tinkeringjoe/bread-modular/opt/Breakouts/PT8211/PT8211.kicad_pcb

## KiCad design opt/Breakouts/PT8211/PT8211.kicad_pcb (2025-01-01)

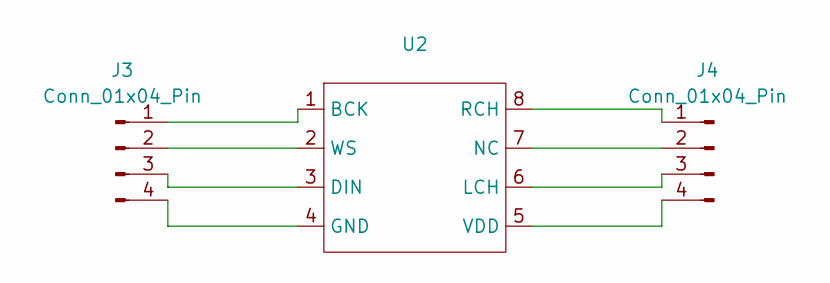
[picture p37: schematic PT8211.kicad_sch]

Parts:
J3, J4: Conn_01x04_Pin; PinSocket_1x04_P2.54mm_Vertical
U2: SOIC-8-1EP_3.9x4.9mm_P1.27mm_EP2.29x3mm

Connections:
unnamed: J3.1, U2.1 (BCK)
unnamed: J3.2, U2.2 (WS)
unnamed: J3.3, U2.3 (DIN)
unnamed: J3.4, U2.4 (GND)
unnamed: J4.1, U2.8 (RCH)
unnamed: J4.2, U2.7 (NC)
unnamed: J4.3, U2.6 (LCH)
unnamed: J4.4, U2.5 (VDD)

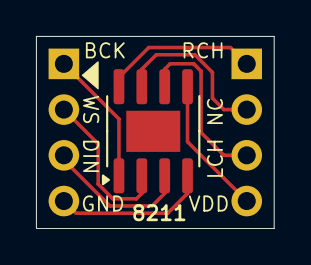
[picture p38: board PT8211.kicad_pcb from above]

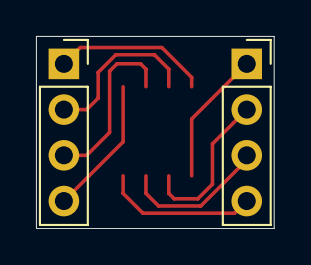
[picture p39: board PT8211.kicad_pcb from below]

Board: 2 copper layers, 13.2 x 10.7 mm, 3 parts (2 on the bottom side), 8 nets.
