tinkeringjoe/bread-modular/opt/Breakouts/Opamps/opamps.kicad_pcb

## KiCad design opt/Breakouts/Opamps/opamps.kicad_pcb (2024-10-20)

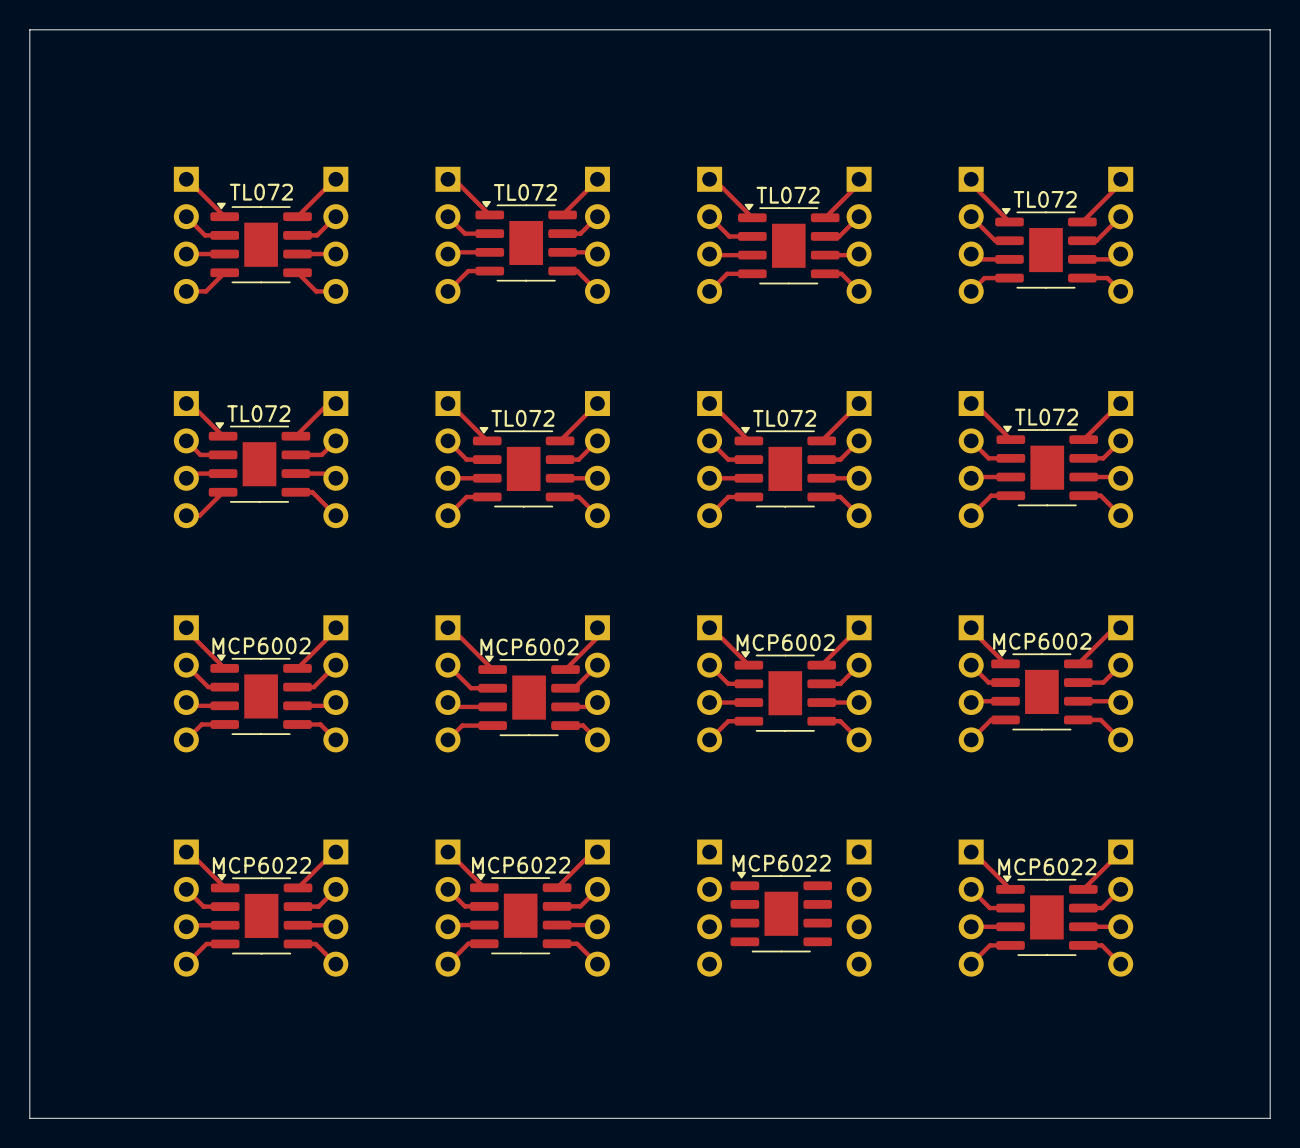
[picture p40: board opamps.kicad_pcb from above]

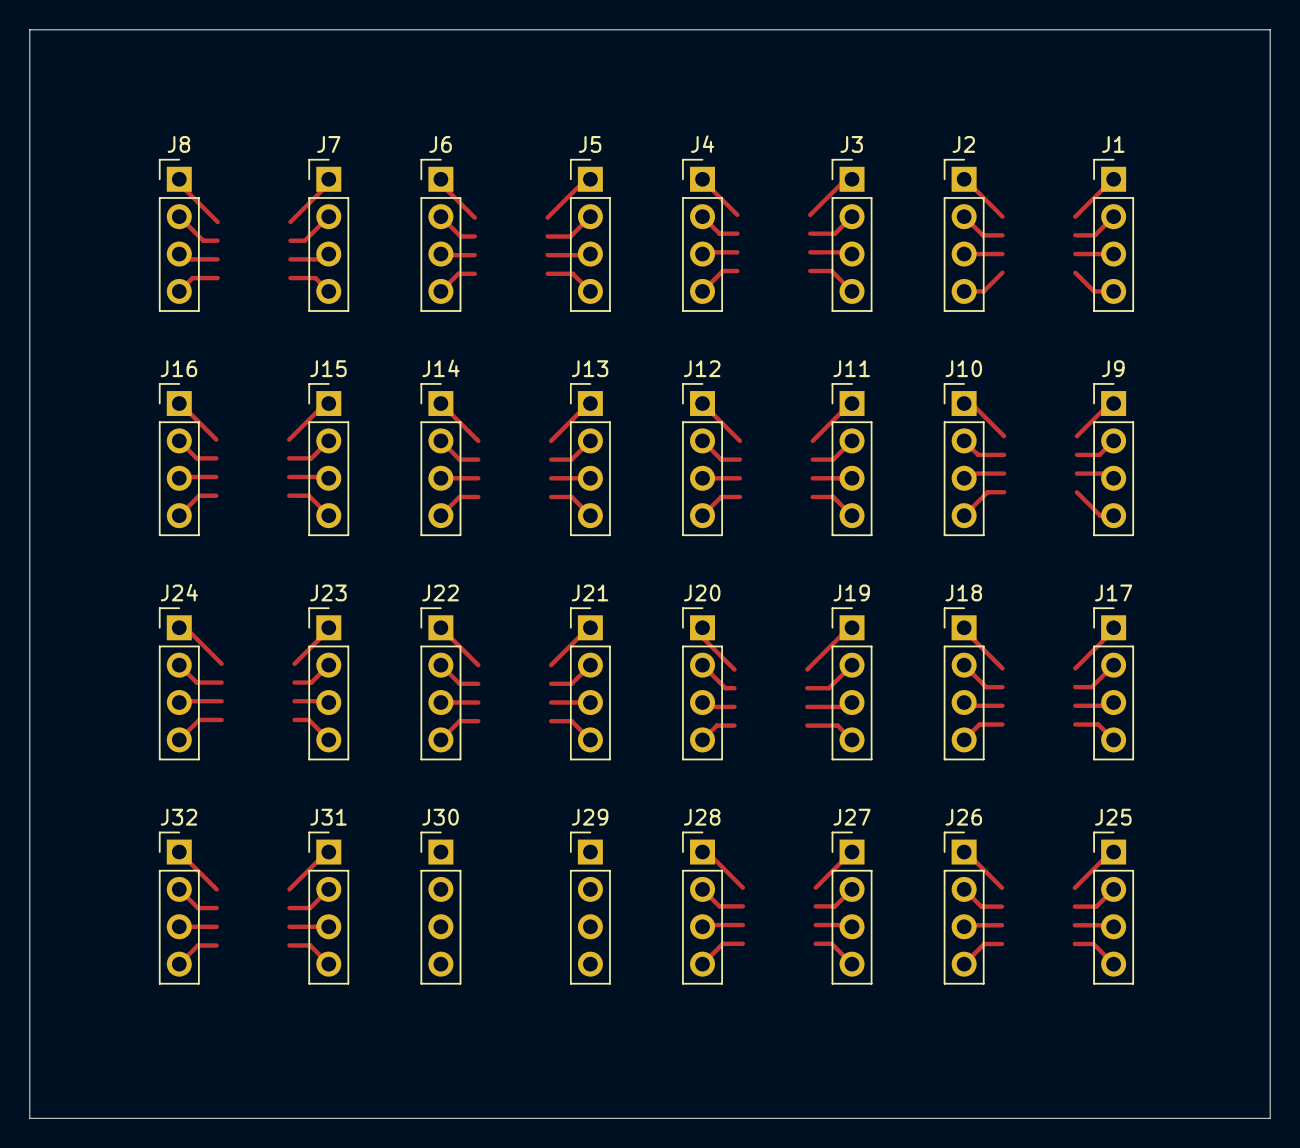
[picture p41: board opamps.kicad_pcb from below]

Board: 2 copper layers, 84.3 x 74.0 mm, 48 parts (32 on the bottom side), 128 nets.

Parts:
J1, J2, J3, J4, J5, J6, J7, J8, J9, J10, J11, J12, J13, J14, J15, J16, J17, J18, J19, J20, J21, J22, J23, J24, J25, J26, J27, J28, J29, J30, J31, J32: Conn_01x04_Pin; PinHeader_1x04_P2.54mm_Vertical
MCP6002, MCP6002#2, MCP6002#3, MCP6002#4: MCP6002-xSN; SOIC-8-1EP_3.9x4.9mm_P1.27mm_EP2.29x3mm
MCP6022, MCP6022#2, MCP6022#3, MCP6022#4: MCP6022; SOIC-8-1EP_3.9x4.9mm_P1.27mm_EP2.29x3mm
TL072, TL072#2, TL072#3, TL072#4, TL072#5, TL072#6, TL072#7, TL072#8: TL072; SOIC-8-1EP_3.9x4.9mm_P1.27mm_EP2.29x3mm

Connections:
unnamed: J1.1, TL072.1
unnamed: J1.2, TL072.2 (-)
unnamed: J1.3, TL072.3 (+)
unnamed: J1.4, TL072.4 (V-)
unnamed: J2.1, TL072.8 (V+)
unnamed: J2.2, TL072.7
unnamed: J2.3, TL072.6 (-)
unnamed: J2.4, TL072.5 (+)
unnamed: J3.1, TL072#2.1
unnamed: J3.2, TL072#2.2 (-)
unnamed: J3.3, TL072#2.3 (+)
unnamed: J3.4, TL072#2.4 (V-)
unnamed: J4.1, TL072#2.8 (V+)
unnamed: J4.2, TL072#2.7
unnamed: J4.3, TL072#2.6 (-)
unnamed: J4.4, TL072#2.5 (+)
unnamed: J5.1, TL072#6.1
unnamed: J5.2, TL072#6.2 (-)
unnamed: J5.3, TL072#6.3 (+)
unnamed: J5.4, TL072#6.4 (V-)
unnamed: J6.1, TL072#6.8 (V+)
unnamed: J6.2, TL072#6.7
unnamed: J6.3, TL072#6.6 (-)
unnamed: J6.4, TL072#6.5 (+)
unnamed: J7.1, TL072#3.1
unnamed: J7.2, TL072#3.2 (-)
unnamed: J7.3, TL072#3.3 (+)
unnamed: J7.4, TL072#3.4 (V-)
unnamed: J8.1, TL072#3.8 (V+)
unnamed: J8.2, TL072#3.7
unnamed: J8.3, TL072#3.6 (-)
unnamed: J8.4, TL072#3.5 (+)
unnamed: J9.1, TL072#8.1
unnamed: J9.2, TL072#8.2 (-)
unnamed: J9.3, TL072#8.3 (+)
unnamed: J9.4, TL072#8.4 (V-)
unnamed: J10.1, TL072#8.8 (V+)
unnamed: J10.2, TL072#8.7
unnamed: J10.3, TL072#8.6 (-)
unnamed: J10.4, TL072#8.5 (+)
unnamed: J11.1, TL072#4.1
unnamed: J11.2, TL072#4.2 (-)
unnamed: J11.3, TL072#4.3 (+)
unnamed: J11.4, TL072#4.4 (V-)
unnamed: J12.1, TL072#4.8 (V+)
unnamed: J12.2, TL072#4.7
unnamed: J12.3, TL072#4.6 (-)
unnamed: J12.4, TL072#4.5 (+)
unnamed: J13.1, TL072#7.1
unnamed: J13.2, TL072#7.2 (-)
unnamed: J13.3, TL072#7.3 (+)
unnamed: J13.4, TL072#7.4 (V-)
unnamed: J14.1, TL072#7.8 (V+)
unnamed: J14.2, TL072#7.7
unnamed: J14.3, TL072#7.6 (-)
unnamed: J14.4, TL072#7.5 (+)
unnamed: J15.1, TL072#5.1
unnamed: J15.2, TL072#5.2 (-)
unnamed: J15.3, TL072#5.3 (+)
unnamed: J15.4, TL072#5.4 (V-)
unnamed: J16.1, TL072#5.8 (V+)
unnamed: J16.2, TL072#5.7
unnamed: J16.3, TL072#5.6 (-)
unnamed: J16.4, TL072#5.5 (+)
unnamed: J17.1, MCP6002#3.1
unnamed: J17.2, MCP6002#3.2 (-)
unnamed: J17.3, MCP6002#3.3 (+)
unnamed: J17.4, MCP6002#3.4 (V-)
unnamed: J18.1, MCP6002#3.8 (V+)
unnamed: J18.2, MCP6002#3.7
unnamed: J18.3, MCP6002#3.6 (-)
unnamed: J18.4, MCP6002#3.5 (+)
unnamed: J19.1, MCP6002#2.1
unnamed: J19.2, MCP6002#2.2 (-)
unnamed: J19.3, MCP6002#2.3 (+)
unnamed: J19.4, MCP6002#2.4 (V-)
unnamed: J20.1, MCP6002#2.8 (V+)
unnamed: J20.2, MCP6002#2.7
unnamed: J20.3, MCP6002#2.6 (-)
unnamed: J20.4, MCP6002#2.5 (+)
unnamed: J21.1, MCP6002.1
unnamed: J21.2, MCP6002.2 (-)
unnamed: J21.3, MCP6002.3 (+)
unnamed: J21.4, MCP6002.4 (V-)
unnamed: J22.1, MCP6002.8 (V+)
unnamed: J22.2, MCP6002.7
unnamed: J22.3, MCP6002.6 (-)
unnamed: J22.4, MCP6002.5 (+)
unnamed: J23.1, MCP6002#4.1
unnamed: J23.2, MCP6002#4.2 (-)
unnamed: J23.3, MCP6002#4.3 (+)
unnamed: J23.4, MCP6002#4.4 (V-)
unnamed: J24.1, MCP6002#4.8 (V+)
unnamed: J24.2, MCP6002#4.7
unnamed: J24.3, MCP6002#4.6 (-)
unnamed: J24.4, MCP6002#4.5 (+)
unnamed: J25.1, MCP6022#3.1
unnamed: J25.2, MCP6022#3.2 (-)
unnamed: J25.3, MCP6022#3.3 (+)
unnamed: J25.4, MCP6022#3.4 (V-)
unnamed: J26.1, MCP6022#3.8 (V+)
unnamed: J26.2, MCP6022#3.7
unnamed: J26.3, MCP6022#3.6 (-)
unnamed: J26.4, MCP6022#3.5 (+)
unnamed: J27.1, MCP6022.1
unnamed: J27.2, MCP6022.2 (-)
unnamed: J27.3, MCP6022.3 (+)
unnamed: J27.4, MCP6022.4 (V-)
unnamed: J28.1, MCP6022.8 (V+)
unnamed: J28.2, MCP6022.7
unnamed: J28.3, MCP6022.6 (-)
unnamed: J28.4, MCP6022.5 (+)
unnamed: J29.1, MCP6022#2.1
unnamed: J29.2, MCP6022#2.2 (-)
unnamed: J29.3, MCP6022#2.3 (+)
unnamed: J29.4, MCP6022#2.4 (V-)
unnamed: J30.1, MCP6022#2.8 (V+)
unnamed: J30.2, MCP6022#2.7
unnamed: J30.3, MCP6022#2.6 (-)
unnamed: J30.4, MCP6022#2.5 (+)
unnamed: J31.1, MCP6022#4.1
unnamed: J31.2, MCP6022#4.2 (-)
unnamed: J31.3, MCP6022#4.3 (+)
unnamed: J31.4, MCP6022#4.4 (V-)
unnamed: J32.1, MCP6022#4.8 (V+)
unnamed: J32.2, MCP6022#4.7
unnamed: J32.3, MCP6022#4.6 (-)
unnamed: J32.4, MCP6022#4.5 (+)
