tinkeringjoe/bread-modular/opt/Breakouts/Attiny1616/MCUs.kicad_pcb

## KiCad design opt/Breakouts/Attiny1616/MCUs.kicad_pcb (2024-11-20)

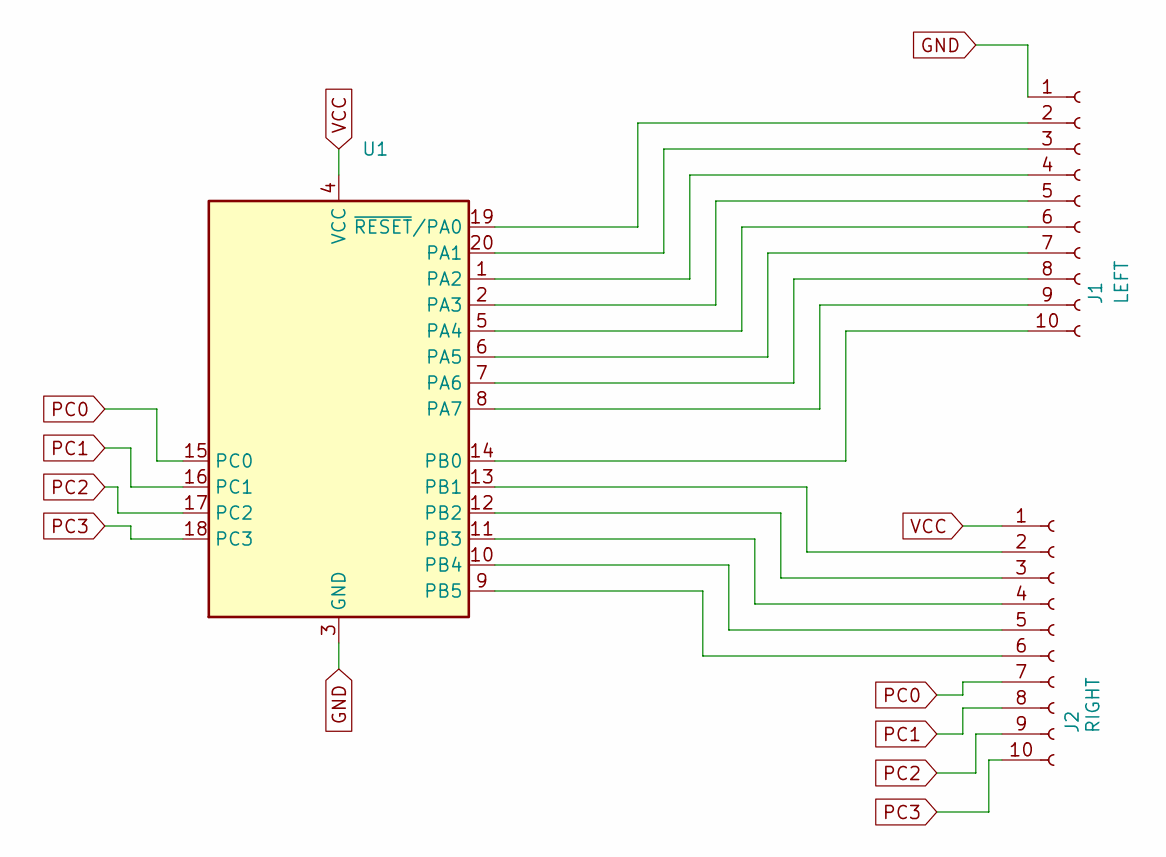
[picture p42: schematic MCUs.kicad_sch]

Parts:
J1: LEFT; PinSocket_1x10_P2.54mm_Vertical
J2: RIGHT; PinSocket_1x10_P2.54mm_Vertical
U1: ATtiny1616-M; VQFN-20-1EP_3x3mm_P0.4mm_EP1.7x1.7mm

Connections:
GND: J1.1, U1.3 (GND), U1.21 (GND)
unnamed: J1.2, U1.19 (~RESET/PA0)
unnamed: J1.3, U1.20 (PA1)
unnamed: J1.4, U1.1 (PA2)
unnamed: J1.5, U1.2 (PA3)
unnamed: J1.6, U1.5 (PA4)
unnamed: J1.7, U1.6 (PA5)
unnamed: J1.8, U1.7 (PA6)
unnamed: J1.9, U1.8 (PA7)
unnamed: J1.10, U1.14 (PB0)
unnamed: J2.2, U1.13 (PB1)
unnamed: J2.3, U1.12 (PB2)
unnamed: J2.4, U1.11 (PB3)
unnamed: J2.5, U1.10 (PB4)
unnamed: J2.6, U1.9 (PB5)
PC0: J2.7, U1.15 (PC0)
PC1: J2.8, U1.16 (PC1)
PC2: J2.9, U1.17 (PC2)
PC3: J2.10, U1.18 (PC3)
VCC: J2.1, U1.4 (VCC)

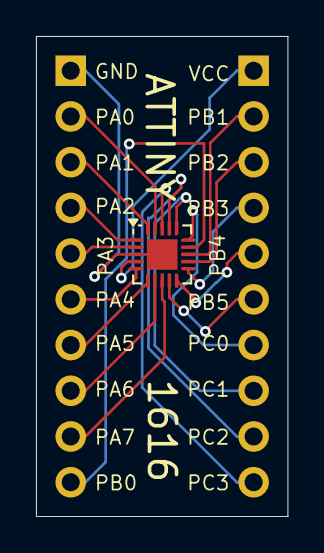
[picture p43: board MCUs.kicad_pcb from above]

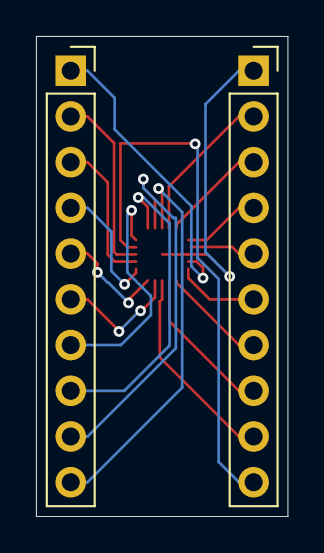
[picture p44: board MCUs.kicad_pcb from below]

Board: 2 copper layers, 14.0 x 26.7 mm, 3 parts (2 on the bottom side), 20 nets.
