tinkeringjoe/bread-modular/modules/drive/drive.kicad_pcb

## KiCad design modules/drive/drive.kicad_pcb (2024-12-27)

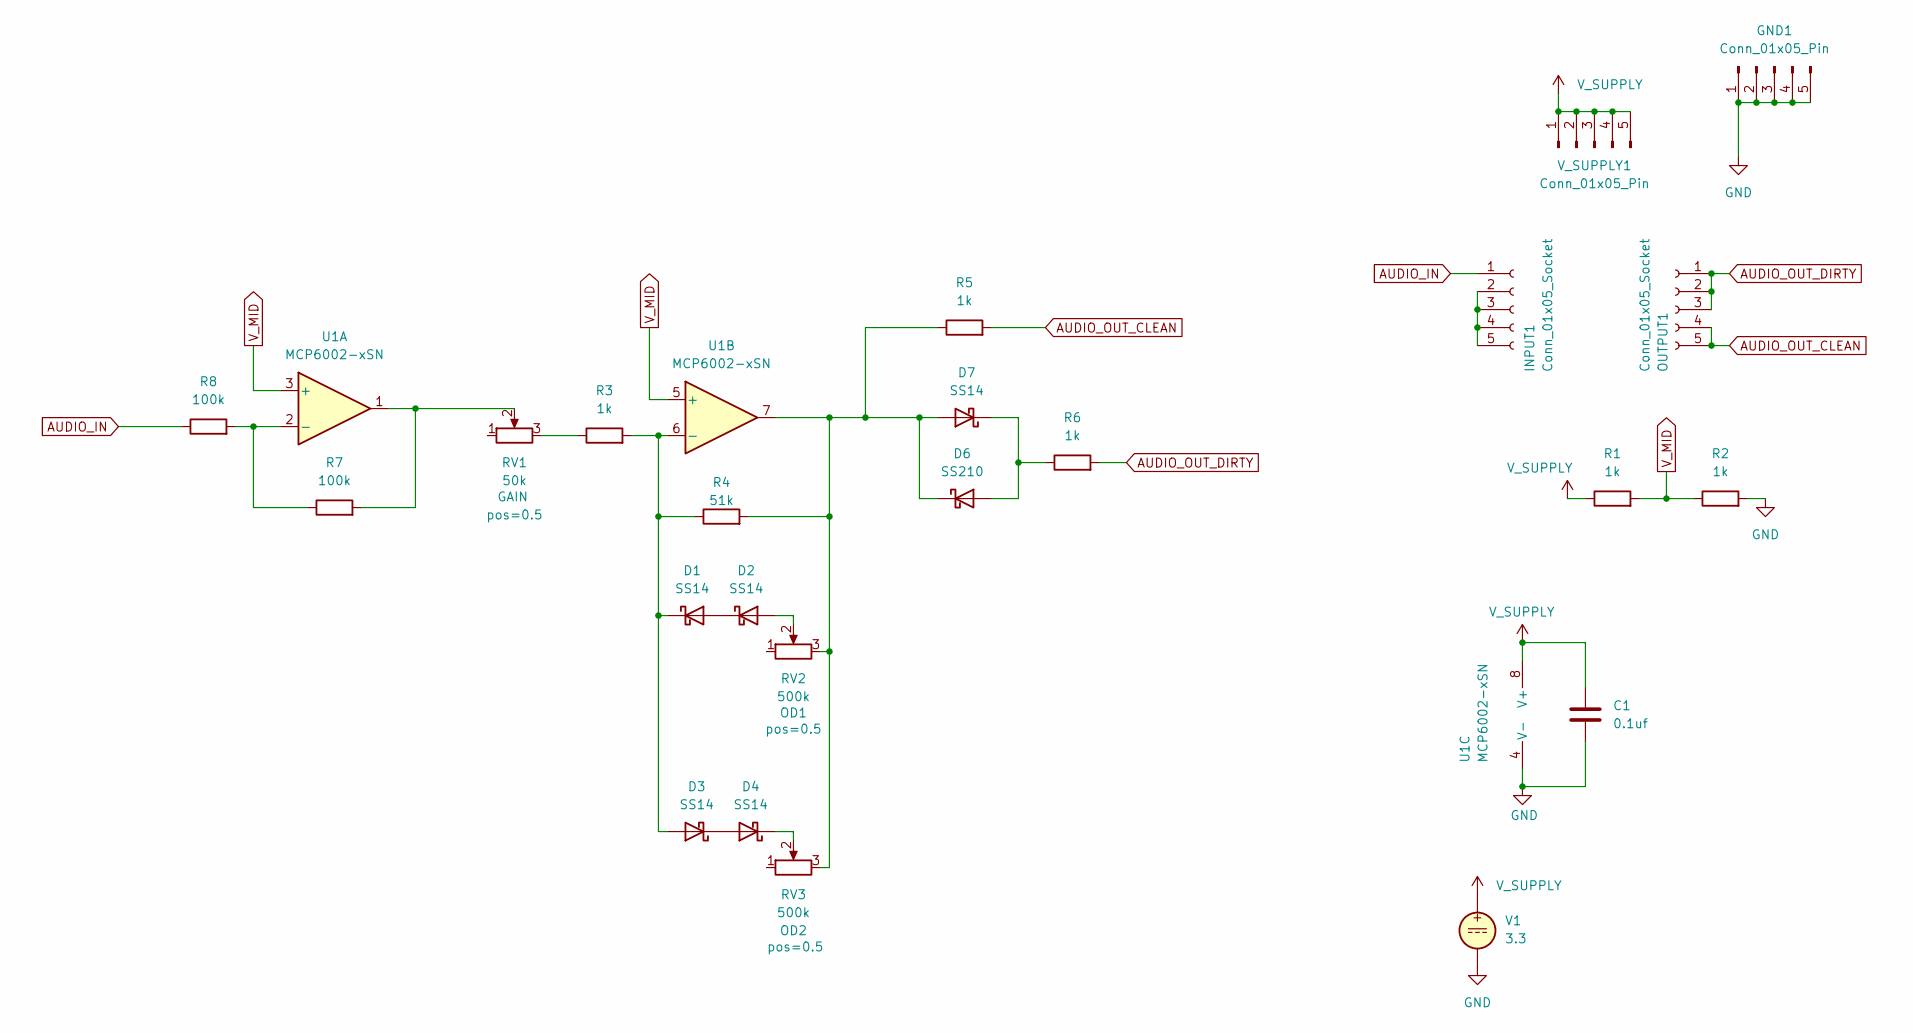
[picture p45: schematic drive.kicad_sch]

Parts:
C1: 0.1uf; C_0402_1005Metric
D1, D2, D3, D4, D7: SS14; D_SMA
D6: SS210; D_SMA
GND1: Conn_01x05_Pin; Power_Connector
INPUT1: Conn_01x05_Socket; PinSocket_1x05_P2.54mm_Vertical
OUTPUT1: Conn_01x05_Socket; PinSocket_1x05_P2.54mm_Vertical
R1, R2, R3, R5, R6: 1k; R_0402_1005Metric
R4: 51k; R_0402_1005Metric
R7, R8: 100k; R_0402_1005Metric
RV1: 50k; Potentiometer_RV09
RV2, RV3: 500k; Potentiometer_RV09
U1: MCP6002-xSN; SOIC-8-1EP_3.9x4.9mm_P1.27mm_EP2.29x3mm
V1: 3.3
V_SUPPLY1: Conn_01x05_Pin; Power_Connector

Connections:
AUDIO_IN: INPUT1.1, R8.1
AUDIO_OUT_CLEAN: OUTPUT1.4, OUTPUT1.5, R5.2
AUDIO_OUT_DIRTY: OUTPUT1.1, OUTPUT1.2, OUTPUT1.3, R6.2
GND: C1.2, GND1.1, GND1.2, GND1.3, GND1.4, GND1.5, R2.2, U1.4 (V-), V1.2
unnamed: D1.2 (A), D2.1 (K)
unnamed: D1.1 (K), D3.2 (A), R3.2, R4.1, U1.6 (-)
unnamed: D2.2 (A), RV2.2
unnamed: D3.1 (K), D4.2 (A)
unnamed: D4.1 (K), RV3.2
unnamed: D6.2 (A), D7.1 (K), R6.1
unnamed: D6.1 (K), D7.2 (A), R4.2, R5.1, RV2.3, RV3.3, U1.7
unnamed: INPUT1.2, INPUT1.3, INPUT1.4, INPUT1.5
unnamed: R3.1, RV1.3
unnamed: R7.2, RV1.2, U1.1
unnamed: R7.1, R8.2, U1.2 (-)
V_MID: R1.2, R2.1, U1.3 (+), U1.5 (+)
V_SUPPLY: C1.1, R1.1, U1.8 (V+), V1.1, V_SUPPLY1.1, V_SUPPLY1.2, V_SUPPLY1.3, V_SUPPLY1.4, V_SUPPLY1.5

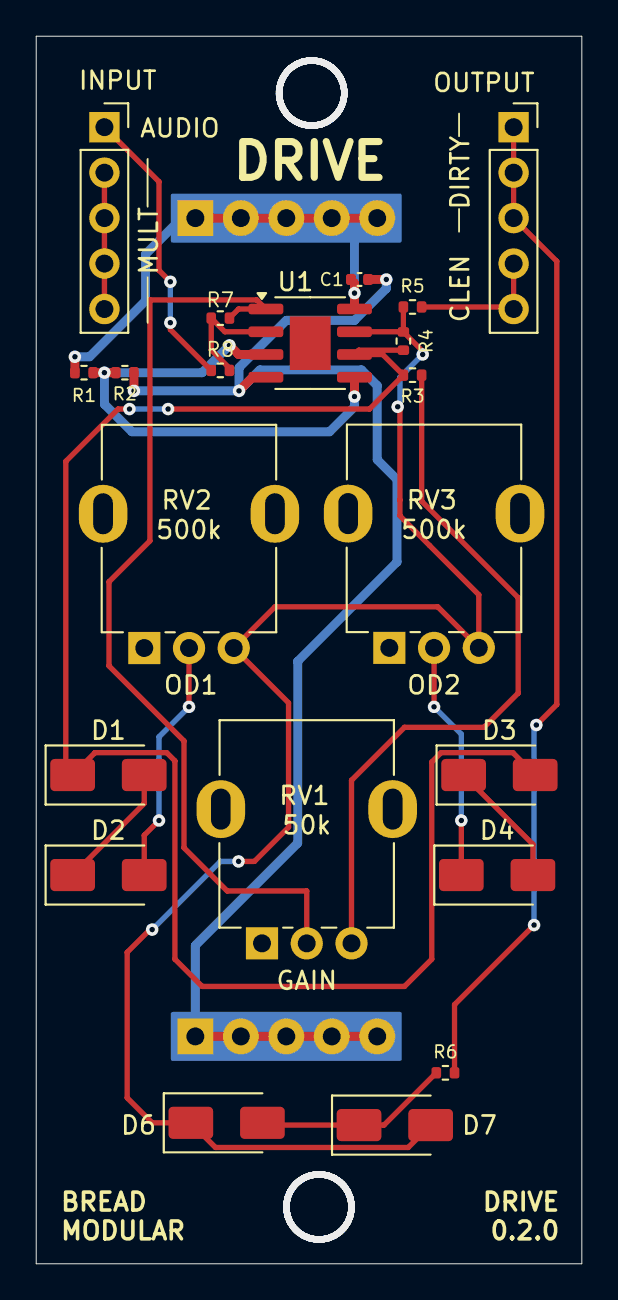
[picture p46: board drive.kicad_pcb from above]

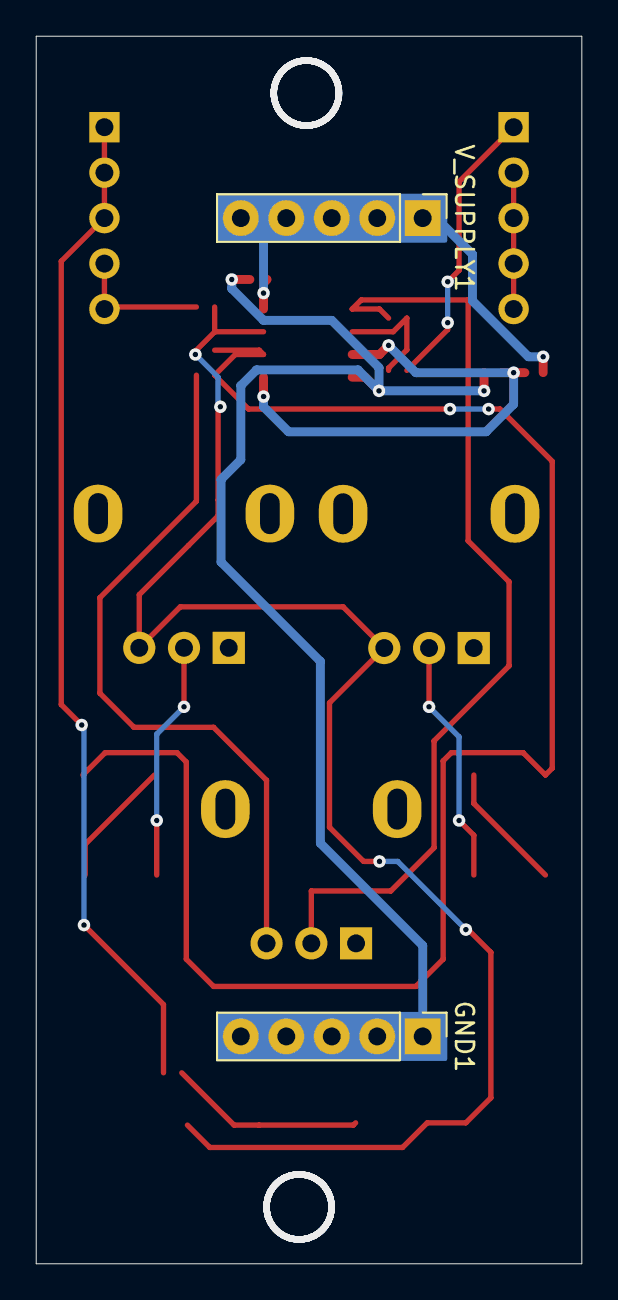
[picture p47: board drive.kicad_pcb from below]

Board: 2 copper layers, 30.5 x 68.6 mm, 23 parts (2 on the bottom side), 17 nets.
