tinkeringjoe/bread-modular/modules/svf/svf.kicad_pcb

## KiCad design modules/svf/svf.kicad_pcb (2024-12-24)

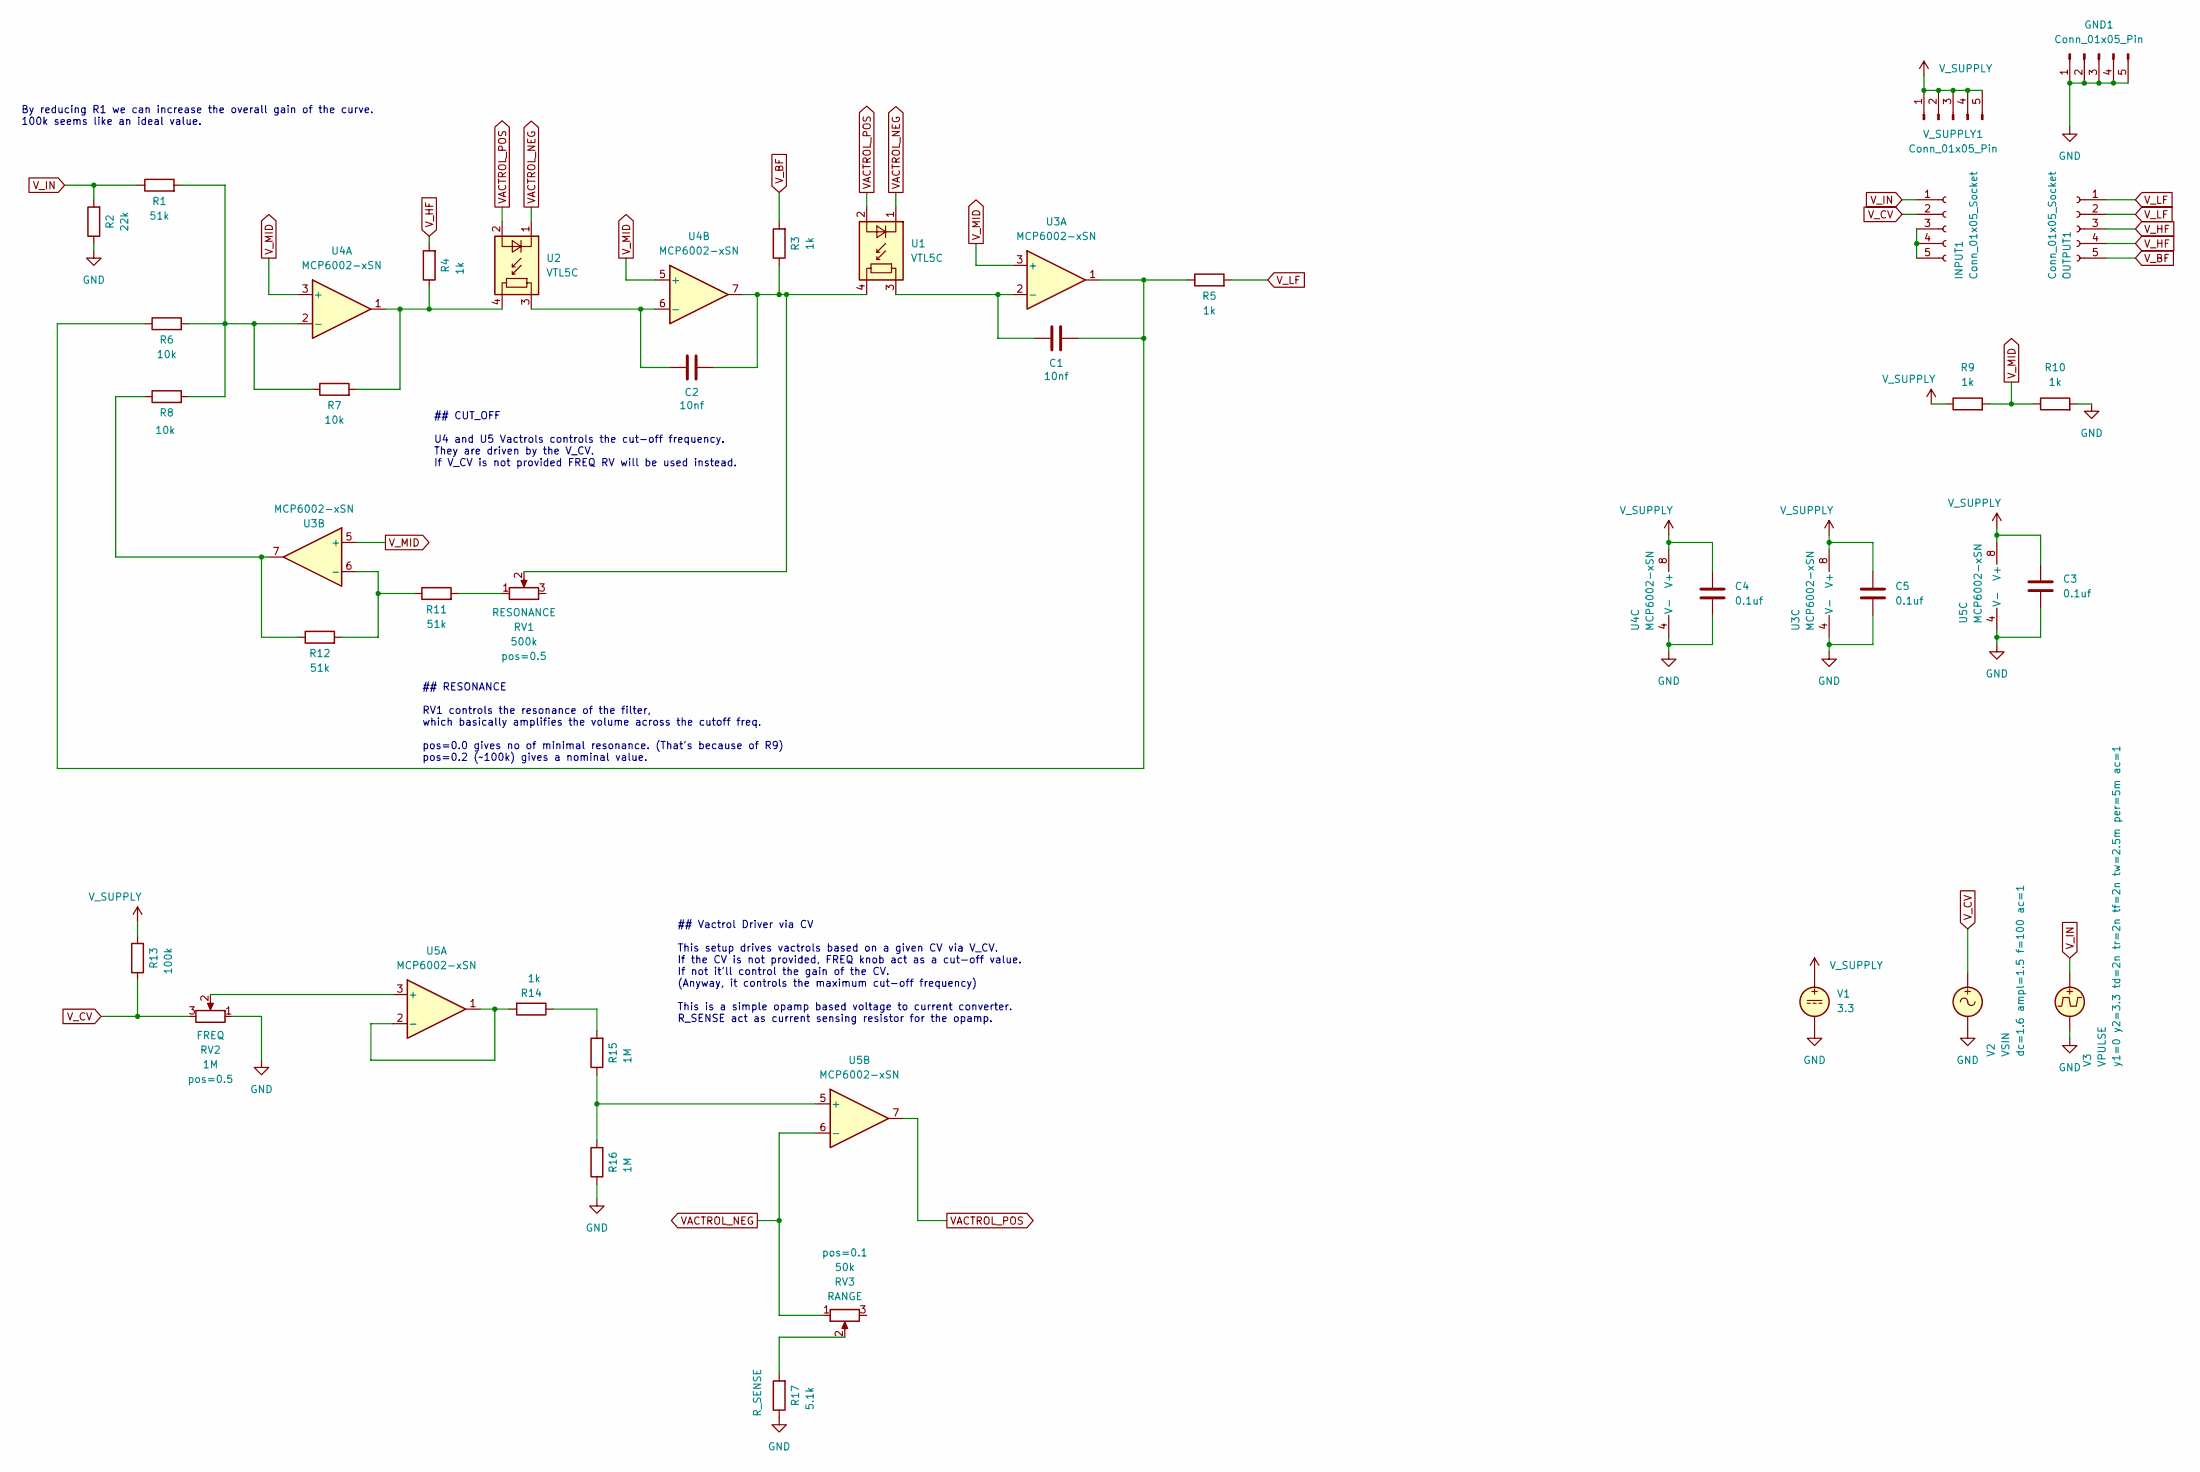
[picture p48: schematic svf.kicad_sch]

Parts:
C1, C2: 10nf; C_0402_1005Metric
C3, C4, C5: 0.1uf; C_0402_1005Metric
GND1: Conn_01x05_Pin; Power_Connector
INPUT1: Conn_01x05_Socket; PinSocket_1x05_P2.54mm_Vertical
OUTPUT1: Conn_01x05_Socket; PinSocket_1x05_P2.54mm_Vertical
R1, R11, R12: 51k; R_0402_1005Metric
R2: 22k; R_0402_1005Metric
R3, R4, R5, R9, R10, R14: 1k; R_0402_1005Metric
R6, R7, R8: 10k; R_0402_1005Metric
R13: 100k; R_0402_1005Metric
R15, R16: 1M; R_0402_1005Metric
R17: 5.1k; R_0402_1005Metric
RV1: 500k; Potentiometer_RV09
RV2: 1M; Potentiometer_RV09
RV3: 50k; Potentiometer_RV09
U1, U2: VTL5C
U3, U4, U5: MCP6002-xSN; SOIC-8-1EP_3.9x4.9mm_P1.27mm_EP2.29x3mm
V1: 3.3
V2: VSIN
V3: VPULSE
V_SUPPLY1: Conn_01x05_Pin; Power_Connector

Connections:
GND: C3.2, C4.2, C5.2, GND1.1, GND1.2, GND1.3, GND1.4, GND1.5, R2.1, R10.2, R16.1, R17.1, RV2.1, U3.4 (V-), U4.4 (V-), U5.4 (V-), V1.2, V2.2, V3.2
unnamed: C1.2, R5.1, R6.1, U3.1
unnamed: C2.2, R3.1, RV1.2, U1.4, U4.7
unnamed: INPUT1.3, INPUT1.4, INPUT1.5
unnamed: R4.1, R7.2, U2.4, U4.1
unnamed: R11.2, RV1.1
unnamed: R8.1, R12.1, U3.7
unnamed: R14.1, R15.2
unnamed: R17.2, RV3.2
unnamed: C1.1, U1.3, U3.2 (-)
unnamed: R11.1, R12.2, U3.6 (-)
unnamed: R1.2, R6.2, R7.1, R8.2, U4.2 (-)
unnamed: C2.1, U2.3, U4.6 (-)
unnamed: RV2.2, U5.3 (+)
unnamed: R14.2, U5.1, U5.2 (-)
unnamed: R15.1, R16.2, U5.5 (+)
VACTROL_NEG: RV3.1, U1.1 (-), U2.1 (-), U5.6 (-)
VACTROL_POS: U1.2 (+), U2.2 (+), U5.7
V_BF: OUTPUT1.5, R3.2
V_CV: INPUT1.2, R13.1, RV2.3, V2.1
V_HF: OUTPUT1.3, OUTPUT1.4, R4.2
V_IN: INPUT1.1, R1.1, R2.2, V3.1
V_LF: OUTPUT1.1, OUTPUT1.2, R5.2
V_MID: R9.2, R10.1, U3.3 (+), U3.5 (+), U4.3 (+), U4.5 (+)
V_SUPPLY: C3.1, C4.1, C5.1, R9.1, R13.2, U3.8 (V+), U4.8 (V+), U5.8 (V+), V1.1, V_SUPPLY1.1, V_SUPPLY1.2, V_SUPPLY1.3, V_SUPPLY1.4, V_SUPPLY1.5

Notes on the sheet:
## Vactrol Driver via CV This setup drives vactrols based on a given CV via V_CV. If the CV is not provided, FREQ knob act as a cut-off value. If not it'll control the gain of the CV. (Anyway, it controls the maximum cut-off frequency) This is a simple opamp based voltage to current converter. R_SE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
## CUT_OFF U4 and U5 Vactrols controls the cut-off frequency. They are driven by the V_CV. If V_CV is not provided FREQ RV will be used instead.
## RESONANCE RV1 controls the resonance of the filter, which basically amplifies the volume across the cutoff freq. pos=0.0 gives no of minimal resonance. (That's because of R9) pos=0.2 (~100k) gives a nominal value.
By reducing R1 we can increase the overall gain of the curve. 100k seems like an ideal value.

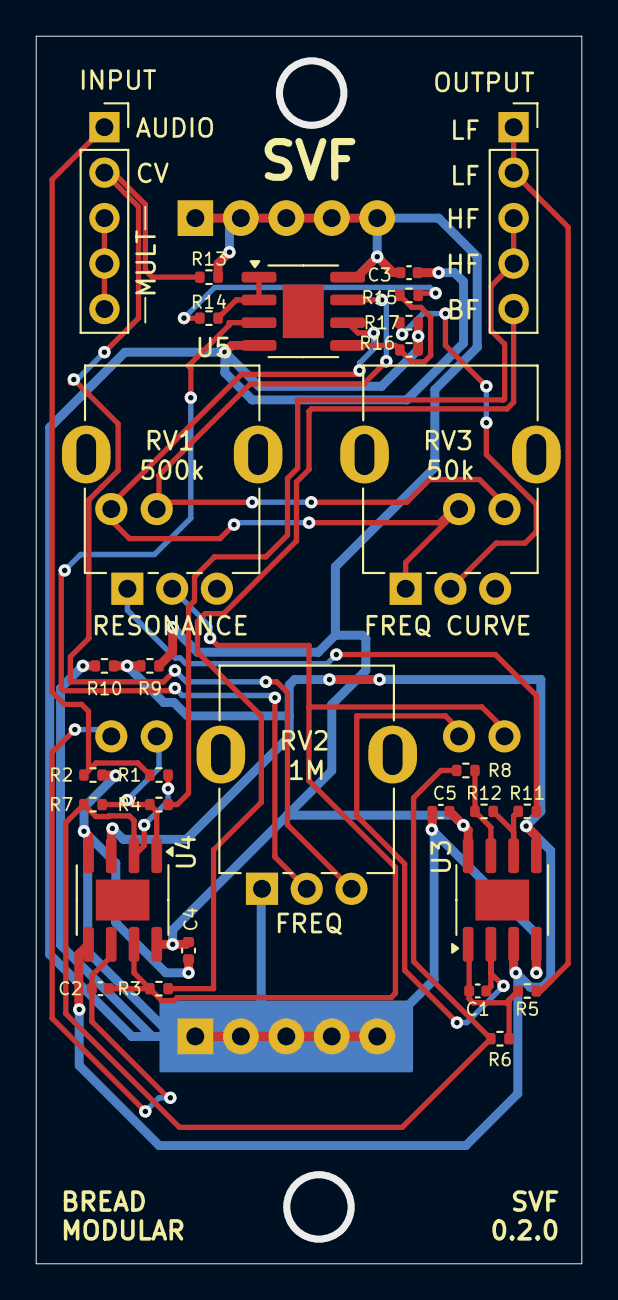
[picture p49: board svf.kicad_pcb from above]

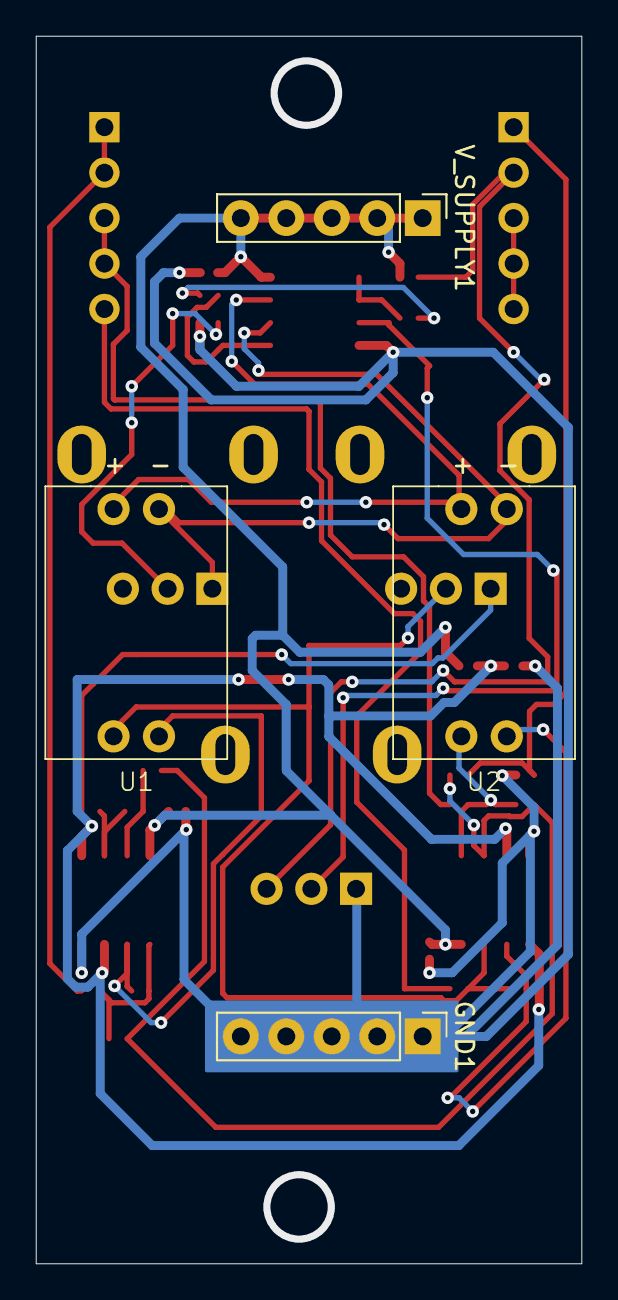
[picture p50: board svf.kicad_pcb from below]

Board: 2 copper layers, 30.5 x 68.6 mm, 34 parts (4 on the bottom side), 25 nets.
