tinkeringjoe/bread-modular/modules/blank/blank.kicad_pcb

## KiCad design modules/blank/blank.kicad_pcb (2024-12-21)

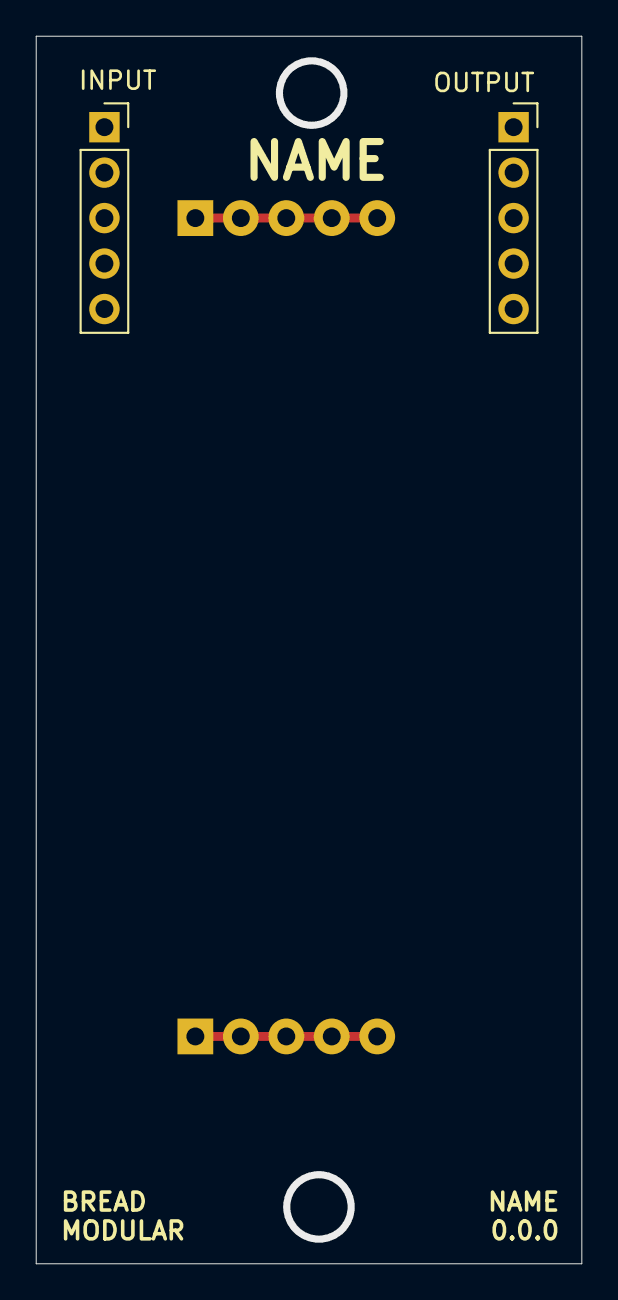
[picture p51: board blank.kicad_pcb from above]

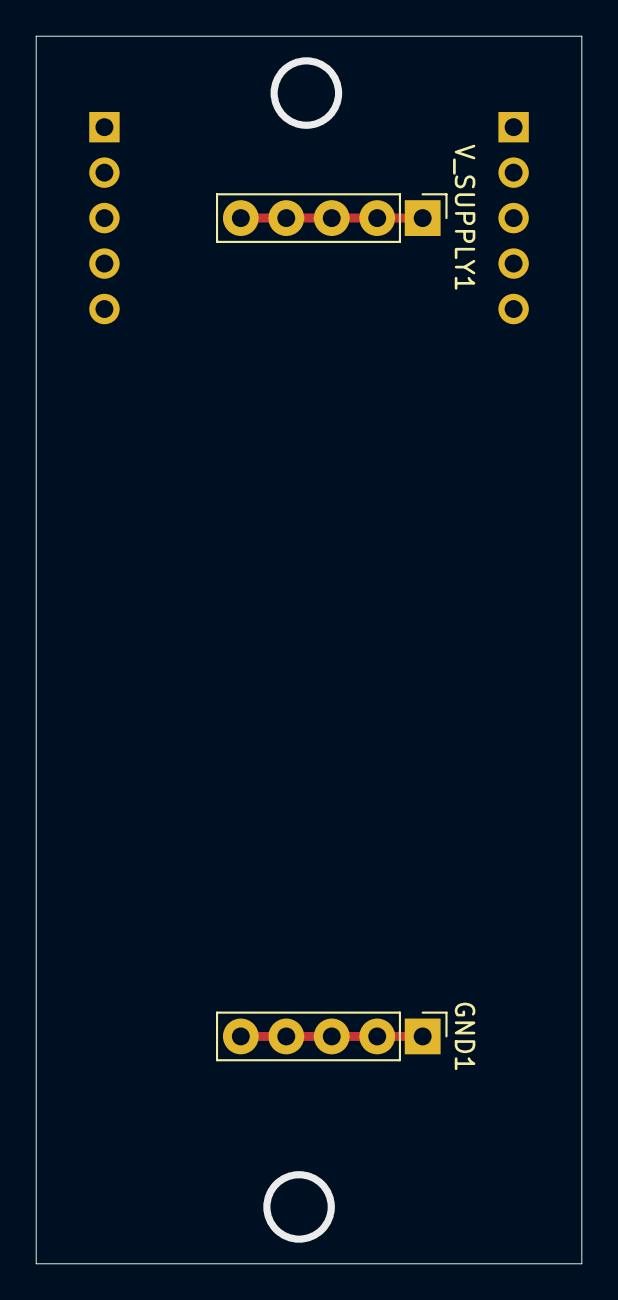
[picture p52: board blank.kicad_pcb from below]

Board: 2 copper layers, 30.5 x 68.6 mm, 4 parts (2 on the bottom side), 2 nets.

Parts:
GND1: Conn_01x05_Pin; Power_Connector
INPUT1: Conn_01x05_Socket; PinSocket_1x05_P2.54mm_Vertical
OUTPUT1: Conn_01x05_Socket; PinSocket_1x05_P2.54mm_Vertical
V_SUPPLY1: Conn_01x05_Pin; Power_Connector

Connections:
GND: GND1.1, GND1.2, GND1.3, GND1.4, GND1.5
V_SUPPLY: V_SUPPLY1.1, V_SUPPLY1.2, V_SUPPLY1.3, V_SUPPLY1.4, V_SUPPLY1.5
