tinkeringjoe/bread-modular/modules/cv_math/cv_math.kicad_pcb

## KiCad design modules/cv_math/cv_math.kicad_pcb (2024-12-15)

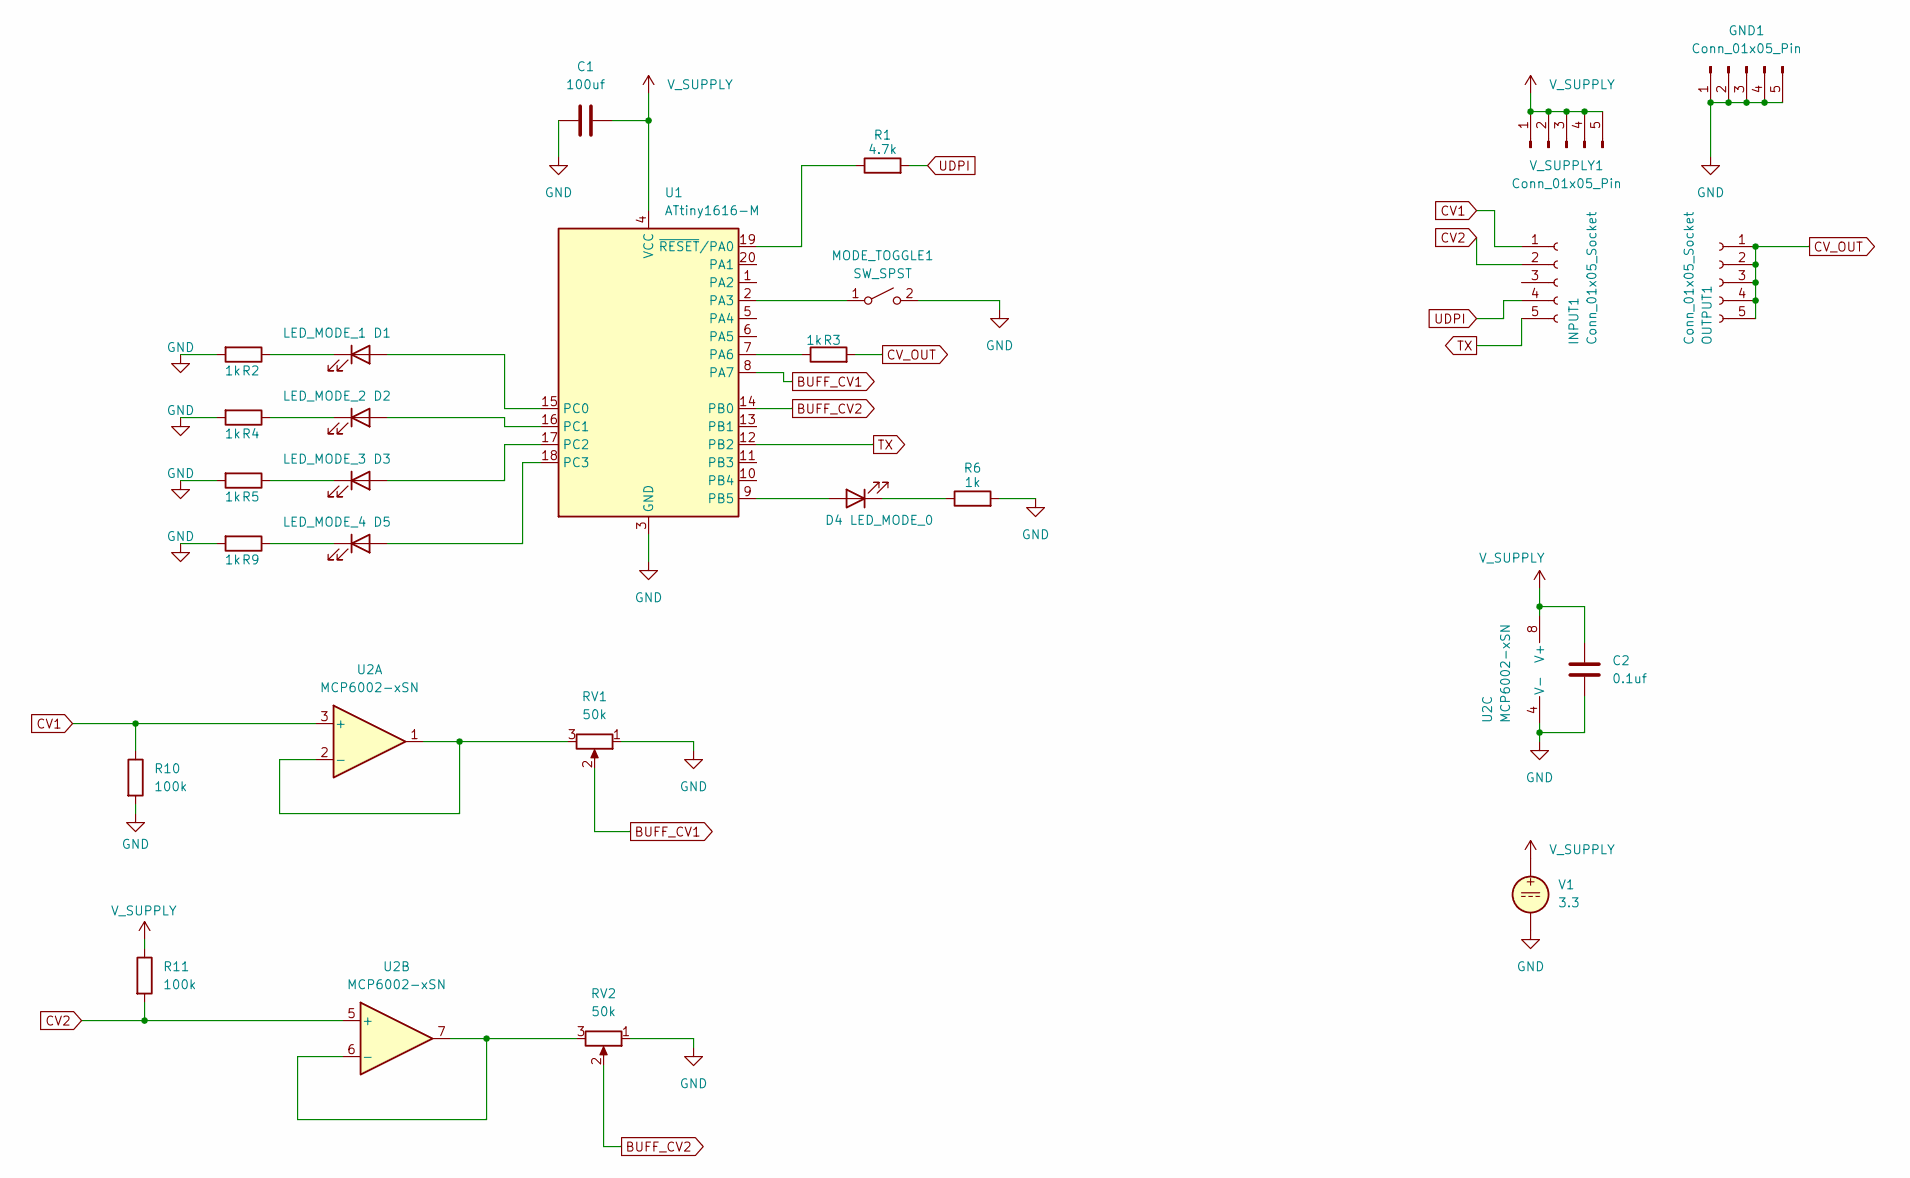
[picture p53: schematic cv_math.kicad_sch]

Parts:
C1: 100uf; C_1206_3216Metric
C2: 0.1uf; C_0402_1005Metric
D1: LED_MODE_1; LED_0603_1608Metric
D2: LED_MODE_2; LED_0603_1608Metric
D3: LED_MODE_3; LED_0603_1608Metric
D4: LED_MODE_0; LED_0603_1608Metric
D5: LED_MODE_4; LED_0603_1608Metric
GND1: Conn_01x05_Pin; Power_Connector
INPUT1: Conn_01x05_Socket; PinSocket_1x05_P2.54mm_Vertical
MODE_TOGGLE1: SW_SPST; SPST_TS-1187A-B-A-B
OUTPUT1: Conn_01x05_Socket; PinSocket_1x05_P2.54mm_Vertical
R1: 4.7k; R_0402_1005Metric
R2, R3, R4, R5, R6, R9: 1k; R_0402_1005Metric
R10, R11: 100k; R_0402_1005Metric
RV1, RV2: 50k; Potentiometer_RV09
U1: ATtiny1616-M; VQFN-20-1EP_3x3mm_P0.4mm_EP1.7x1.7mm
U2: MCP6002-xSN; SOIC-8-1EP_3.9x4.9mm_P1.27mm_EP2.29x3mm
V1: 3.3
V_SUPPLY1: Conn_01x05_Pin; Power_Connector

Connections:
BUFF_CV1: RV1.2, U1.8 (PA7)
BUFF_CV2: RV2.2, U1.14 (PB0)
CV1: INPUT1.1, R10.1, U2.3 (+)
CV2: INPUT1.2, R11.2, U2.5 (+)
CV_OUT: OUTPUT1.1, OUTPUT1.2, OUTPUT1.3, OUTPUT1.4, OUTPUT1.5, R3.2
GND: C1.1, C2.2, GND1.1, GND1.2, GND1.3, GND1.4, GND1.5, MODE_TOGGLE1.2 (B), R2.2, R4.2, R5.2, R6.2, R9.2, R10.2, RV1.1, RV2.1, U1.3 (GND), U1.21 (GND), U2.4 (V-), V1.2
unnamed: D1.2 (A), U1.15 (PC0)
unnamed: D1.1 (K), R2.1
unnamed: D2.2 (A), U1.16 (PC1)
unnamed: D2.1 (K), R4.1
unnamed: D3.2 (A), U1.17 (PC2)
unnamed: D3.1 (K), R5.1
unnamed: D4.2 (A), U1.9 (PB5)
unnamed: D4.1 (K), R6.1
unnamed: D5.2 (A), U1.18 (PC3)
unnamed: D5.1 (K), R9.1
unnamed: MODE_TOGGLE1.1 (A), U1.2 (PA3)
unnamed: R3.1, U1.7 (PA6)
unnamed: R1.1, U1.19 (~RESET/PA0)
unnamed: RV1.3, U2.1, U2.2 (-)
unnamed: RV2.3, U2.6 (-), U2.7
TX: INPUT1.5, U1.12 (PB2)
UDPI: INPUT1.4, R1.2
V_SUPPLY: C1.2, C2.1, R11.1, U1.4 (VCC), U2.8 (V+), V1.1, V_SUPPLY1.1, V_SUPPLY1.2, V_SUPPLY1.3, V_SUPPLY1.4, V_SUPPLY1.5

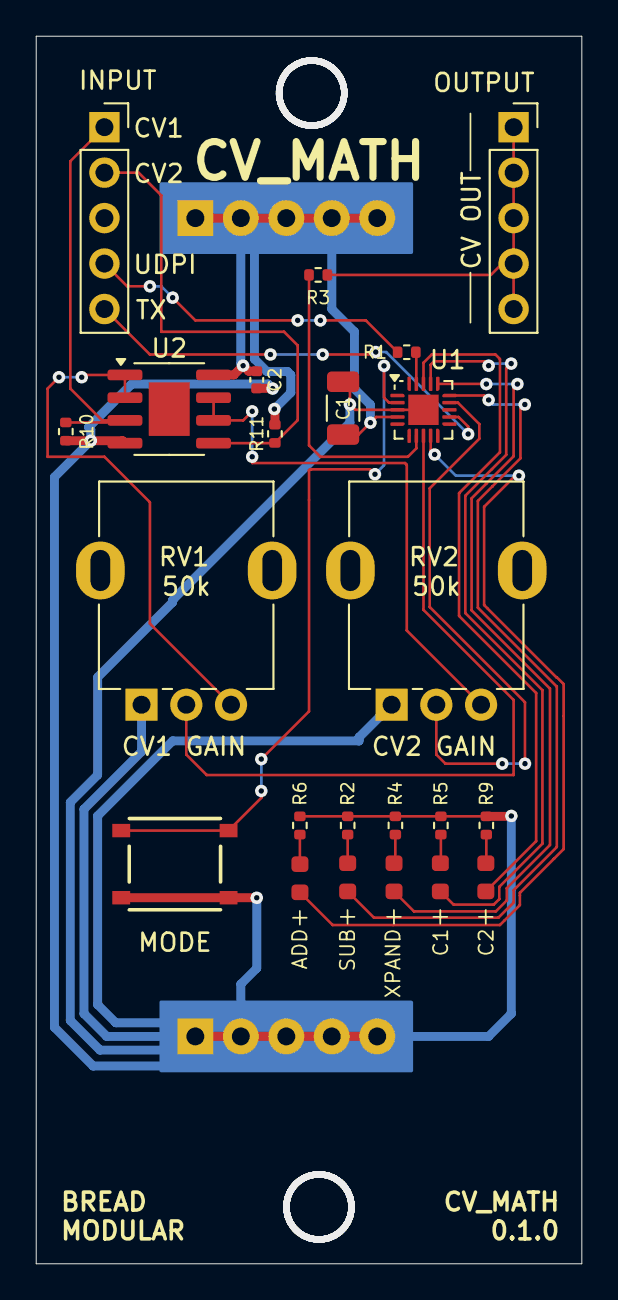
[picture p54: board cv_math.kicad_pcb from above]

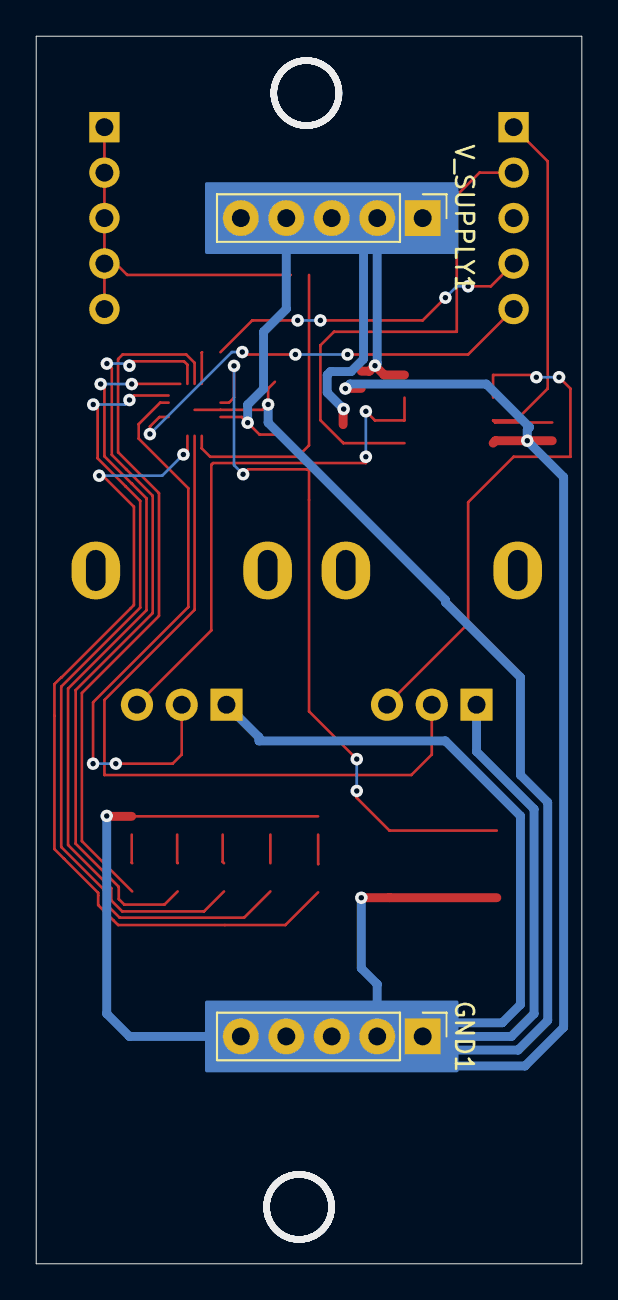
[picture p55: board cv_math.kicad_pcb from below]

Board: 2 copper layers, 30.5 x 68.6 mm, 25 parts (2 on the bottom side), 24 nets.
