tinkeringjoe/bread-modular/modules/noise/noise.kicad_pcb

## KiCad design modules/noise/noise.kicad_pcb (2024-12-09)

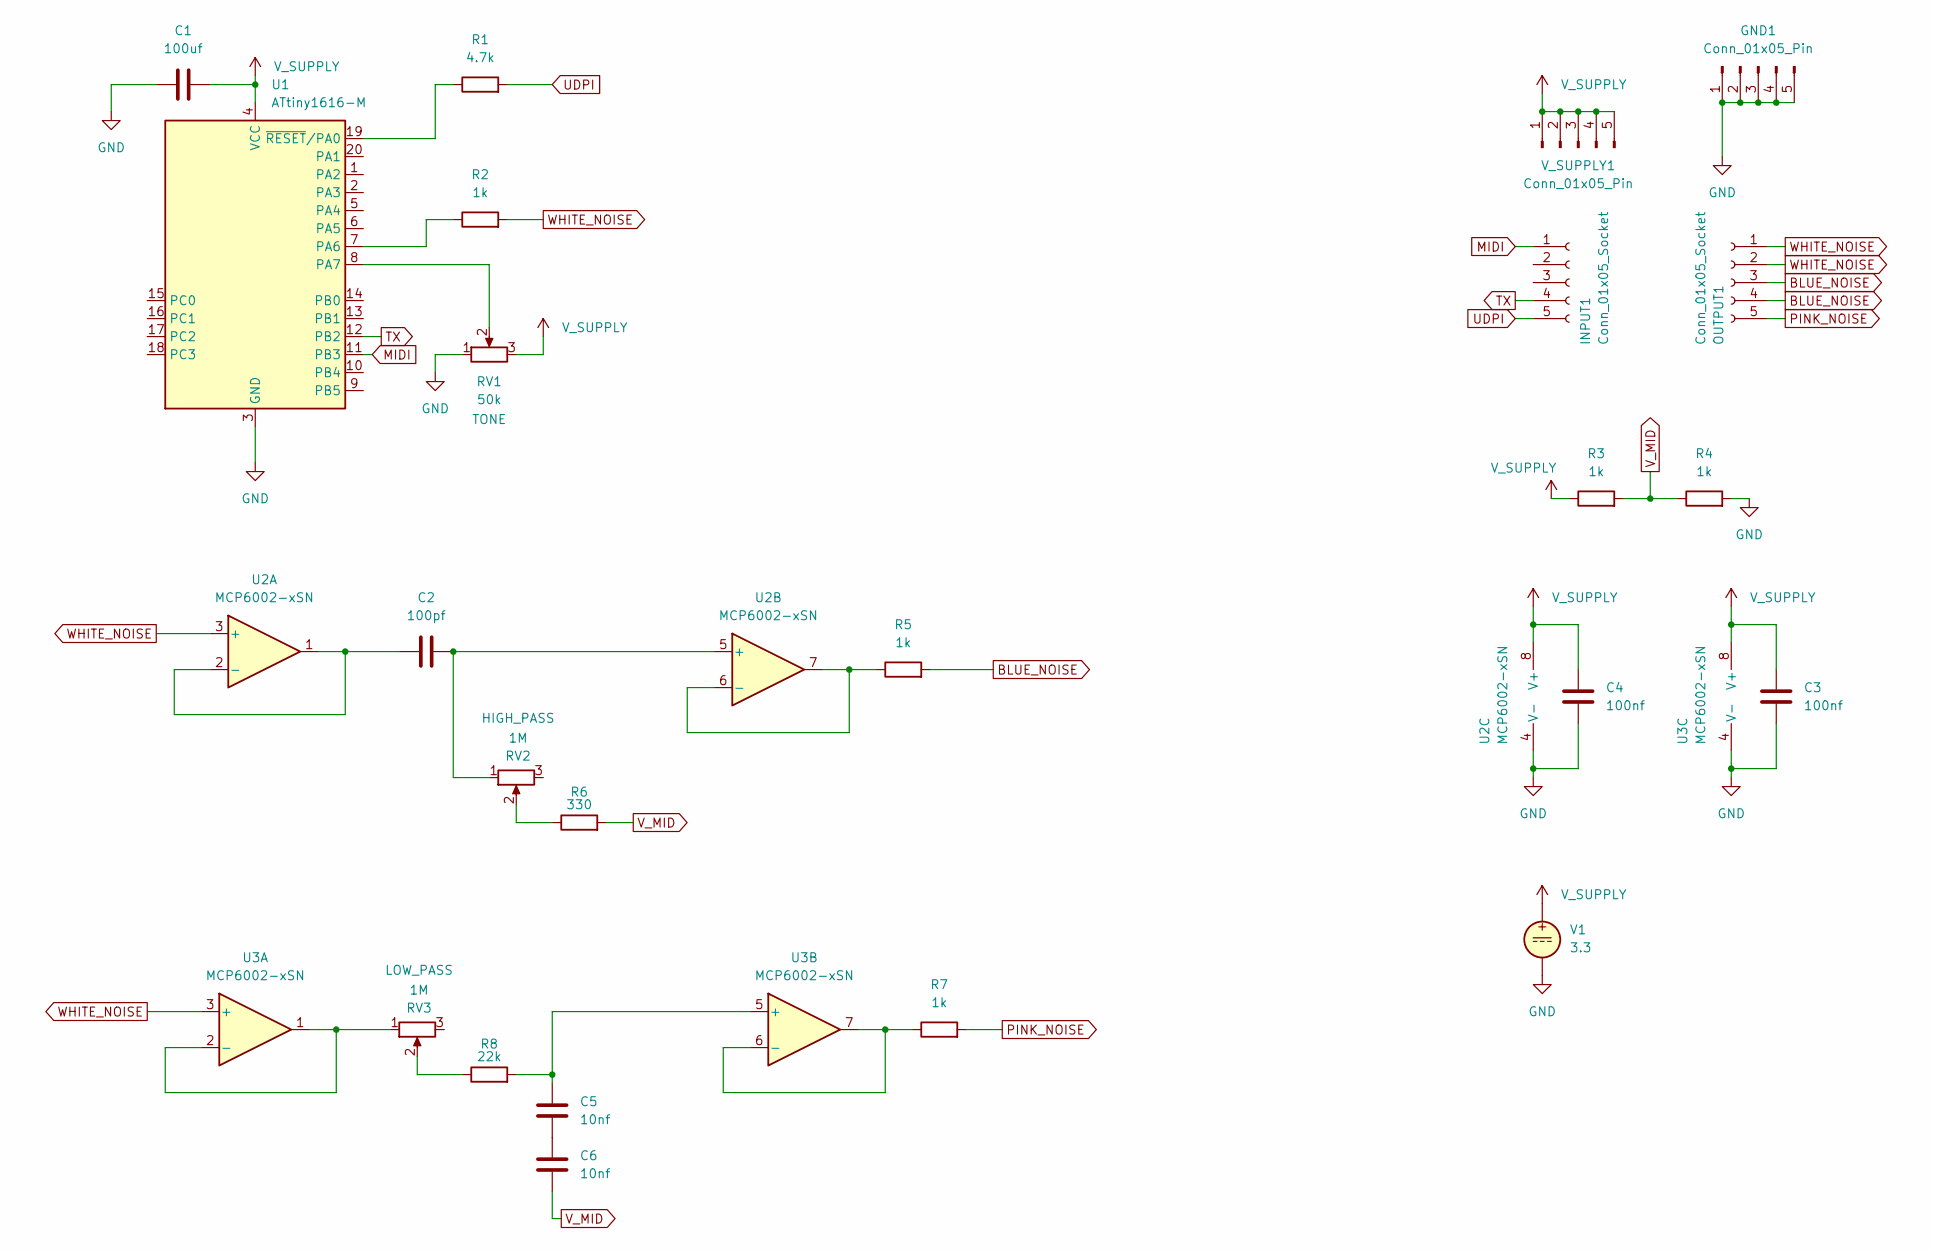
[picture p56: schematic noise.kicad_sch]

Parts:
C1: 100uf; C_1206_3216Metric
C2: 100pf; C_0402_1005Metric
C3, C4: 100nf; C_0402_1005Metric
C5, C6: 10nf; C_0402_1005Metric
GND1: Conn_01x05_Pin; Power_Connector
INPUT1: Conn_01x05_Socket; PinSocket_1x05_P2.54mm_Vertical
OUTPUT1: Conn_01x05_Socket; PinSocket_1x05_P2.54mm_Vertical
R1: 4.7k; R_0402_1005Metric
R2, R3, R4, R5, R7: 1k; R_0402_1005Metric
R6: 330; R_0402_1005Metric
R8: 22k; R_0402_1005Metric
RV1: 50k; Potentiometer_RV09
RV2, RV3: 1M; Potentiometer_RV09
U1: ATtiny1616-M; VQFN-20-1EP_3x3mm_P0.4mm_EP1.7x1.7mm
U2, U3: MCP6002-xSN; SOIC-8-1EP_3.9x4.9mm_P1.27mm_EP2.29x3mm
V1: 3.3
V_SUPPLY1: Conn_01x05_Pin; Power_Connector

Connections:
BLUE_NOISE: OUTPUT1.3, OUTPUT1.4, R5.2
GND: C1.1, C3.1, C4.1, GND1.1, GND1.2, GND1.3, GND1.4, GND1.5, R4.2, RV1.1, U1.3 (GND), U1.21 (GND), U2.4 (V-), U3.4 (V-), V1.2
MIDI: INPUT1.1, U1.11 (PB3)
unnamed: C5.1, C6.2
unnamed: R6.1, RV2.2
unnamed: R8.1, RV3.2
unnamed: R2.1, U1.7 (PA6)
unnamed: RV1.2, U1.8 (PA7)
unnamed: R1.1, U1.19 (~RESET/PA0)
unnamed: C2.1, U2.1, U2.2 (-)
unnamed: C2.2, RV2.1, U2.5 (+)
unnamed: R5.1, U2.6 (-), U2.7
unnamed: RV3.1, U3.1, U3.2 (-)
unnamed: C5.2, R8.2, U3.5 (+)
unnamed: R7.1, U3.6 (-), U3.7
PINK_NOISE: OUTPUT1.5, R7.2
TX: INPUT1.4, U1.12 (PB2)
UDPI: INPUT1.5, R1.2
V_MID: C6.1, R3.2, R4.1, R6.2
V_SUPPLY: C1.2, C3.2, C4.2, R3.1, RV1.3, U1.4 (VCC), U2.8 (V+), U3.8 (V+), V1.1, V_SUPPLY1.1, V_SUPPLY1.2, V_SUPPLY1.3, V_SUPPLY1.4, V_SUPPLY1.5
WHITE_NOISE: OUTPUT1.1, OUTPUT1.2, R2.2, U2.3 (+), U3.3 (+)

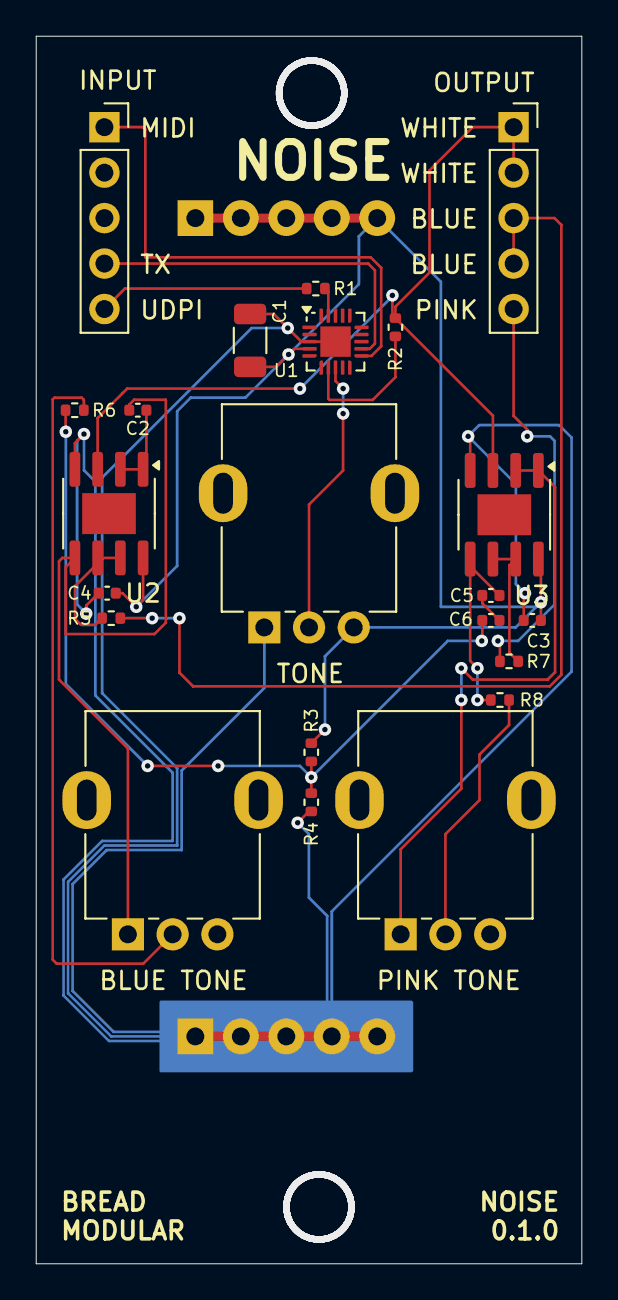
[picture p57: board noise.kicad_pcb from above]

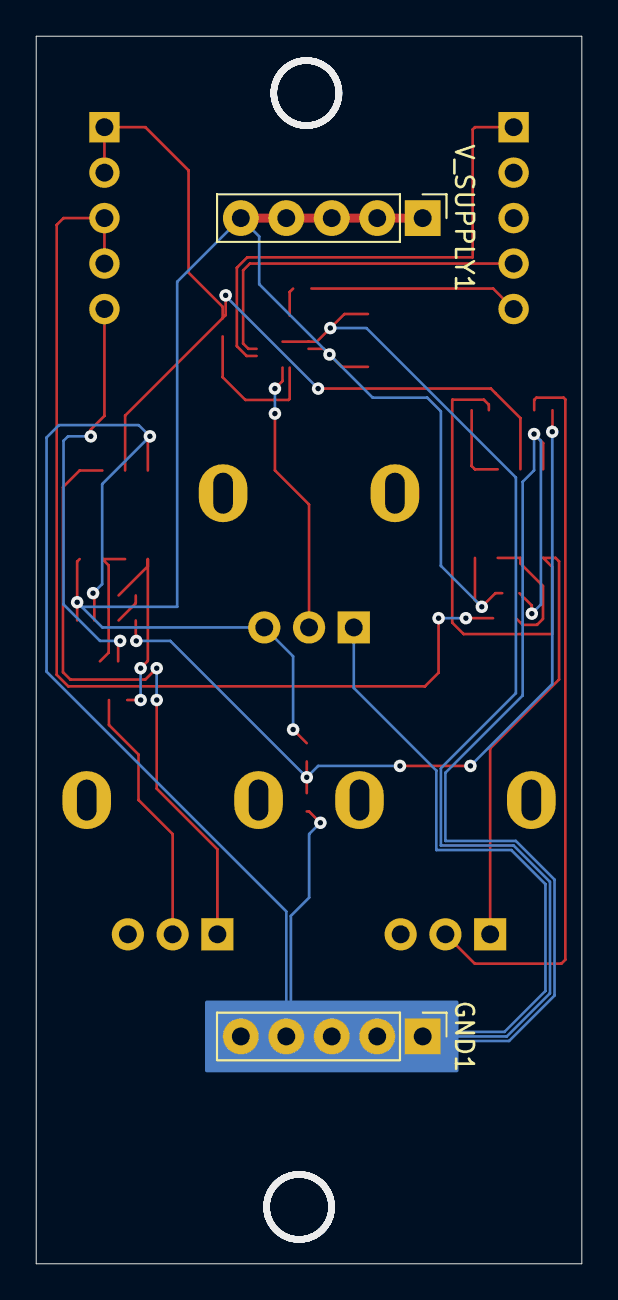
[picture p58: board noise.kicad_pcb from below]

Board: 2 copper layers, 30.5 x 68.6 mm, 24 parts (2 on the bottom side), 21 nets.
