tinkeringjoe/bread-modular/modules/usb_power/usb_power.kicad_pcb

## KiCad design modules/usb_power/usb_power.kicad_pcb (2024-11-24)

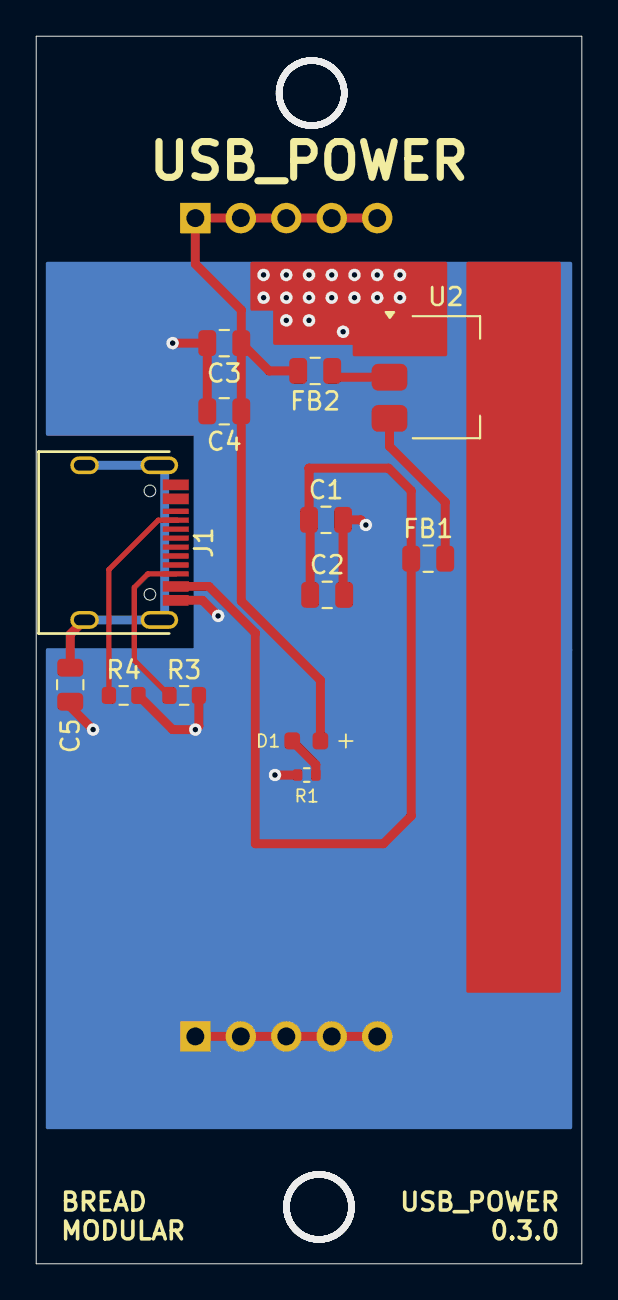
[picture p59: board usb_power.kicad_pcb from above]

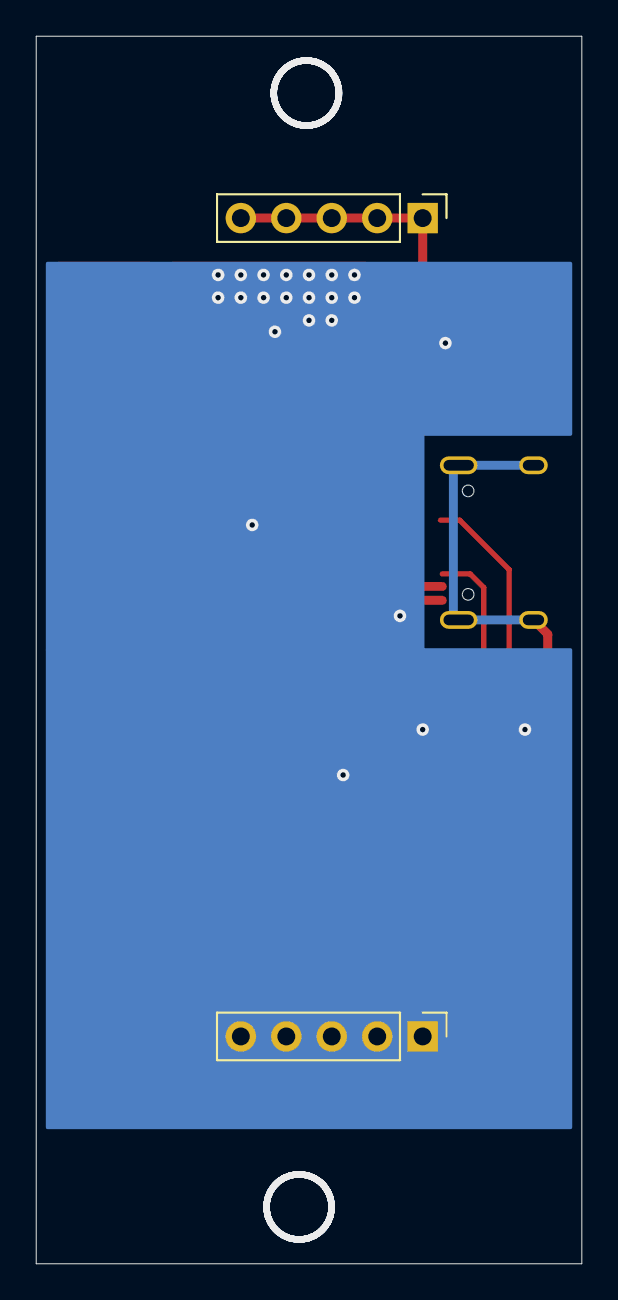
[picture p60: board usb_power.kicad_pcb from below]

Board: 2 copper layers, 30.5 x 68.6 mm, 15 parts (2 on the bottom side), 9 nets.

Parts:
5V1: Conn_01x05_Pin; PinHeader_1x05_P2.54mm_Vertical
C1, C3: 10uf; C_0805_2012Metric
C2, C4: 0.1uf; C_0805_2012Metric
C5: 10nf; C_0805_2012Metric
D1: LED; LED_0603_1608Metric
FB1, FB2: GZ2012E800TF; C_0805_2012Metric
GND1: Conn_01x05_Pin; PinHeader_1x05_P2.54mm_Vertical
J1: USB_C_Receptacle_PowerOnly_6P; HRO-TYPE-C-31-M-12
R1: 1k; R_0402_1005Metric
R3, R4: 5.1k; R_0603_1608Metric
U2: AMS1117-3.3; SOT-223

Connections:
+3.3V: 5V1.1, 5V1.2, 5V1.3, 5V1.4, 5V1.5, C3.1, C4.1, D1.2 (A), FB2.2
GND: C1.2, C2.2, C3.2, C4.2, C5.2, GND1.1, GND1.2, GND1.3, GND1.4, GND1.5, J1.A12 (GND), R1.2, R3.2, R4.2, U2.1 (GND)
unnamed: C1.1, C2.1, FB1.1, J1.A9 (VBUS)
unnamed: D1.1 (K), R1.1
unnamed: J1.A5 (CC1), R4.1
unnamed: J1.B5 (CC2), R3.1
unnamed: C5.1, J1.S1 (SHIELD)
unnamed: FB1.2, U2.3 (VI)
unnamed: FB2.1, U2.2 (VO)
