tinkeringjoe/bread-modular/modules/kick/kick.kicad_pcb

## KiCad design modules/kick/kick.kicad_pcb (2024-11-22)

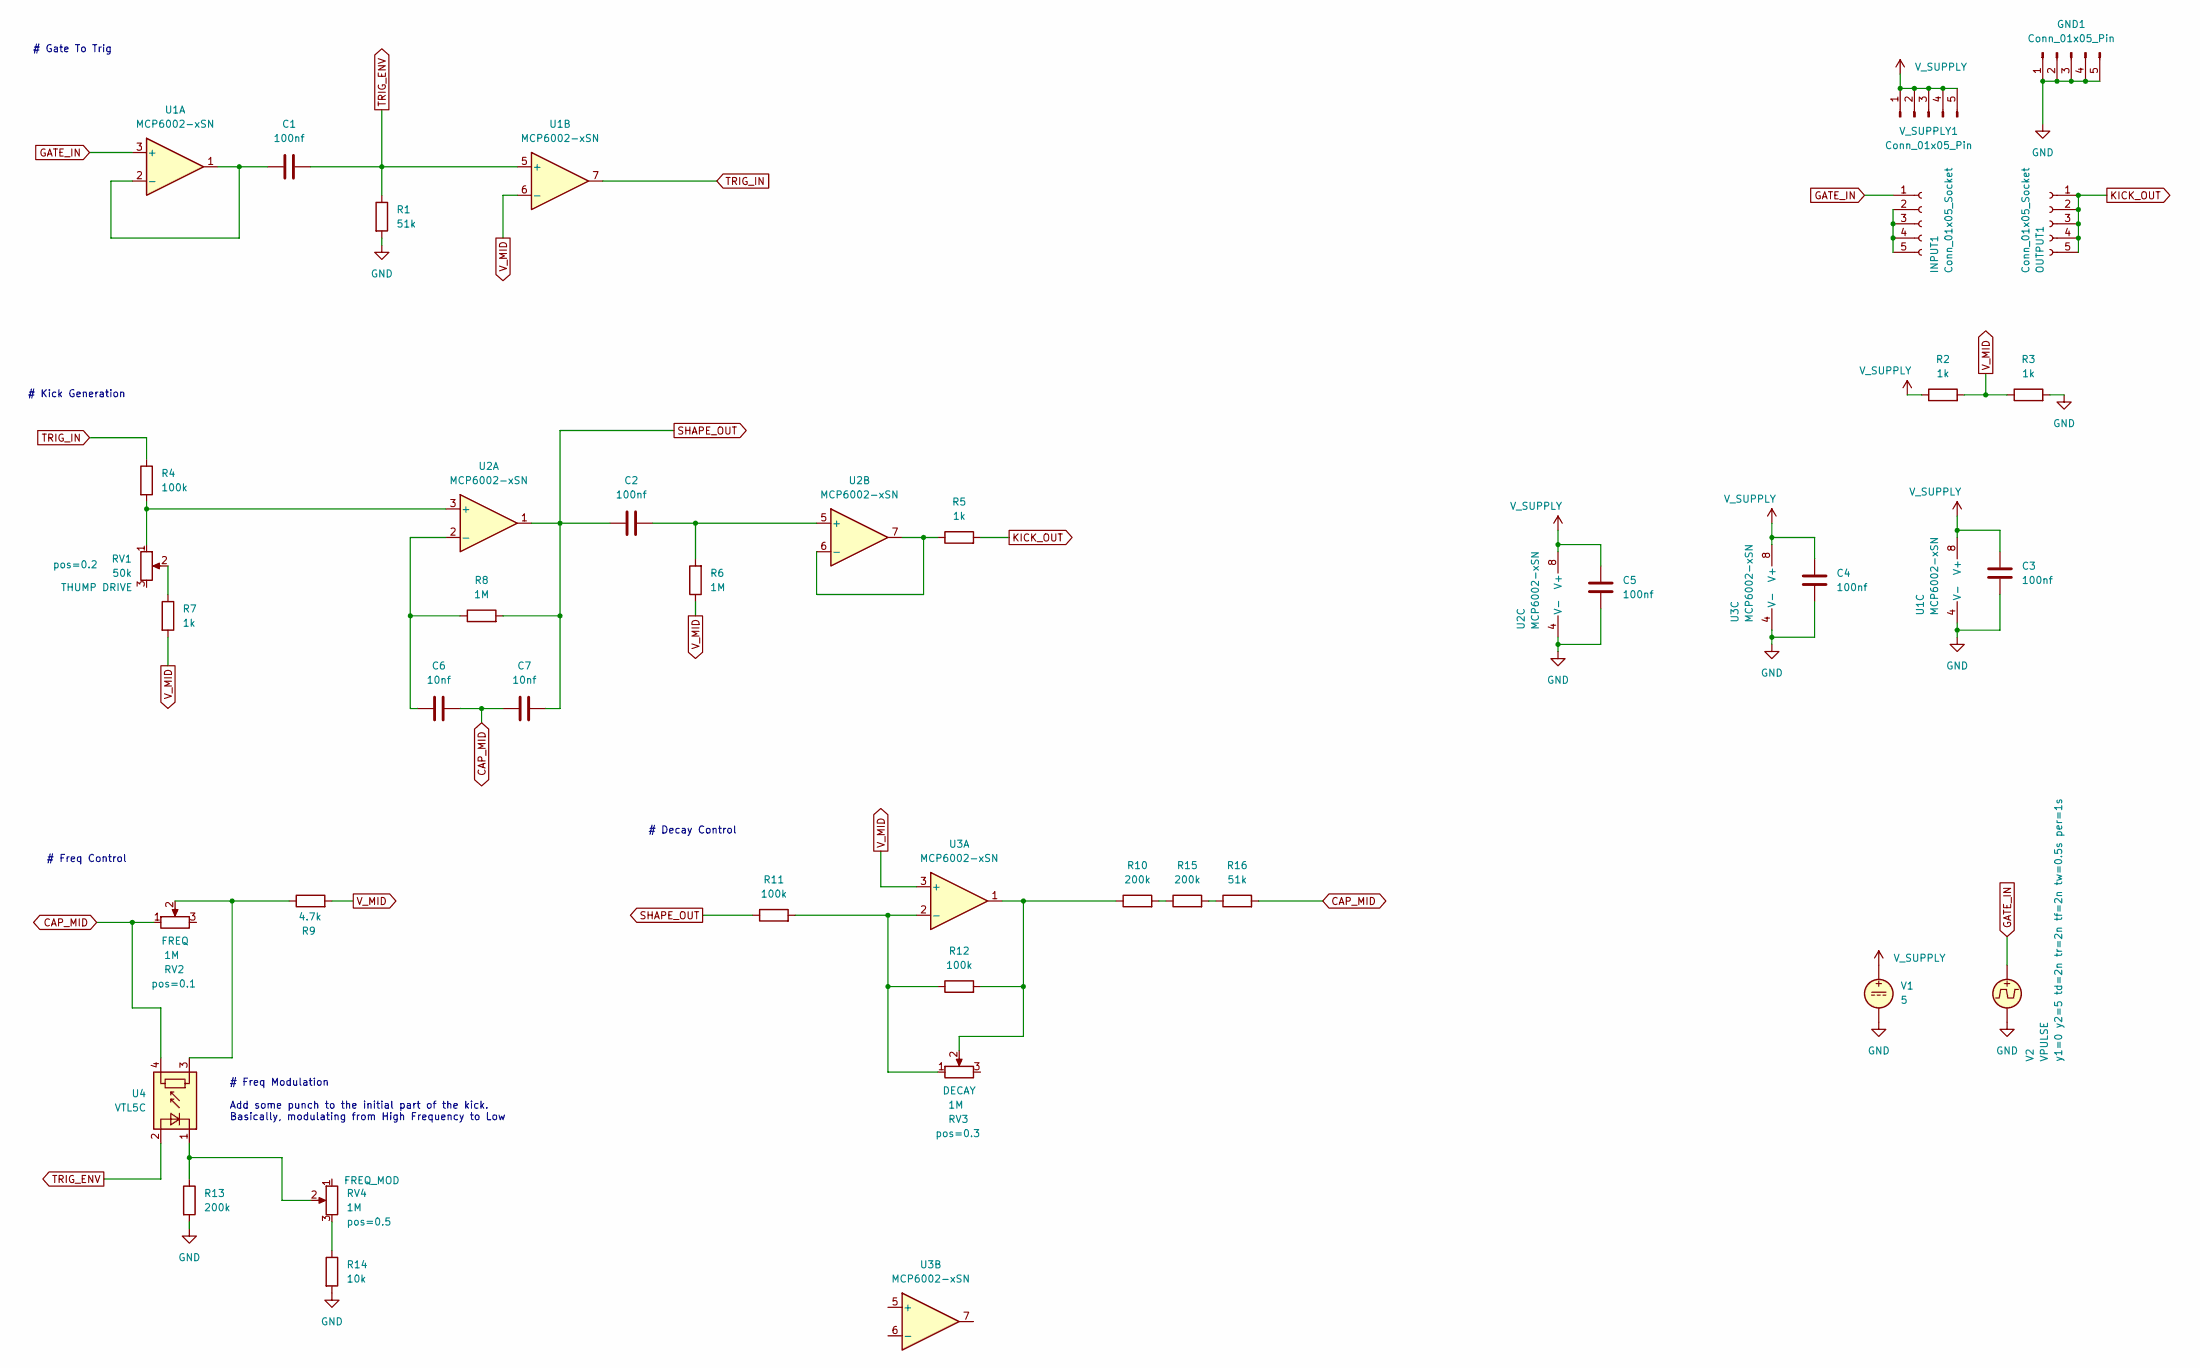
[picture p61: schematic kick.kicad_sch]

Parts:
C1, C2, C3, C4, C5: 100nf; C_0402_1005Metric
C6, C7: 10nf; C_0402_1005Metric
GND1: Conn_01x05_Pin; Power_Connector
INPUT1: Conn_01x05_Socket; PinSocket_1x05_P2.54mm_Vertical
OUTPUT1: Conn_01x05_Socket; PinSocket_1x05_P2.54mm_Vertical
R1, R16: 51k; R_0402_1005Metric
R2, R3, R5, R7: 1k; R_0402_1005Metric
R4, R11, R12: 100k; R_0402_1005Metric
R6, R8: 1M; R_0402_1005Metric
R9: 4.7k; R_0402_1005Metric
R10, R13, R15: 200k; R_0402_1005Metric
R14: 10k; R_0402_1005Metric
RV1: 50k; Potentiometer_RV09
RV2, RV3, RV4: 1M; Potentiometer_RV09
U1, U2, U3: MCP6002-xSN; SOIC-8-1EP_3.9x4.9mm_P1.27mm_EP2.29x3mm
U4: VTL5C
V1: 5
V2: VPULSE
V_SUPPLY1: Conn_01x05_Pin; Power_Connector

Connections:
CAP_MID: C6.2, C7.1, R16.2, RV2.1, U4.4
GATE_IN: INPUT1.1, U1.3 (+), V2.1
GND: C3.2, C4.2, C5.2, GND1.1, GND1.2, GND1.3, GND1.4, GND1.5, R1.2, R3.2, R13.2, R14.2, U1.4 (V-), U2.4 (V-), U3.4 (V-), V1.2, V2.2
KICK_OUT: OUTPUT1.1, OUTPUT1.2, OUTPUT1.3, OUTPUT1.4, OUTPUT1.5, R5.2
unnamed: INPUT1.2, INPUT1.3, INPUT1.4, INPUT1.5
unnamed: R7.1, RV1.2
unnamed: R9.1, RV2.2, U4.3
unnamed: R10.1, R12.2, RV3.2, U3.1
unnamed: R10.2, R15.1
unnamed: R14.1, RV4.3
unnamed: R15.2, R16.1
unnamed: C1.1, U1.1, U1.2 (-)
unnamed: R4.2, RV1.1, U2.3 (+)
unnamed: C6.1, R8.1, U2.2 (-)
unnamed: C2.2, R6.2, U2.5 (+)
unnamed: R5.1, U2.6 (-), U2.7
unnamed: R11.2, R12.1, RV3.1, U3.2 (-)
unnamed: R13.1, RV4.2, U4.1 (-)
SHAPE_OUT: C2.1, C7.2, R8.2, R11.1, U2.1
TRIG_ENV: C1.2, R1.1, U1.5 (+), U4.2 (+)
TRIG_IN: R4.1, U1.7
V_MID: R2.2, R3.1, R6.1, R7.2, R9.2, U1.6 (-), U3.3 (+)
V_SUPPLY: C3.1, C4.1, C5.1, R2.1, U1.8 (V+), U2.8 (V+), U3.8 (V+), V1.1, V_SUPPLY1.1, V_SUPPLY1.2, V_SUPPLY1.3, V_SUPPLY1.4, V_SUPPLY1.5

Notes on the sheet:
# Decay Control
# Gate To Trig
# Freq Control
# Kick Generation
# Freq Modulation Add some punch to the initial part of the kick. Basically, modulating from High Frequency to Low

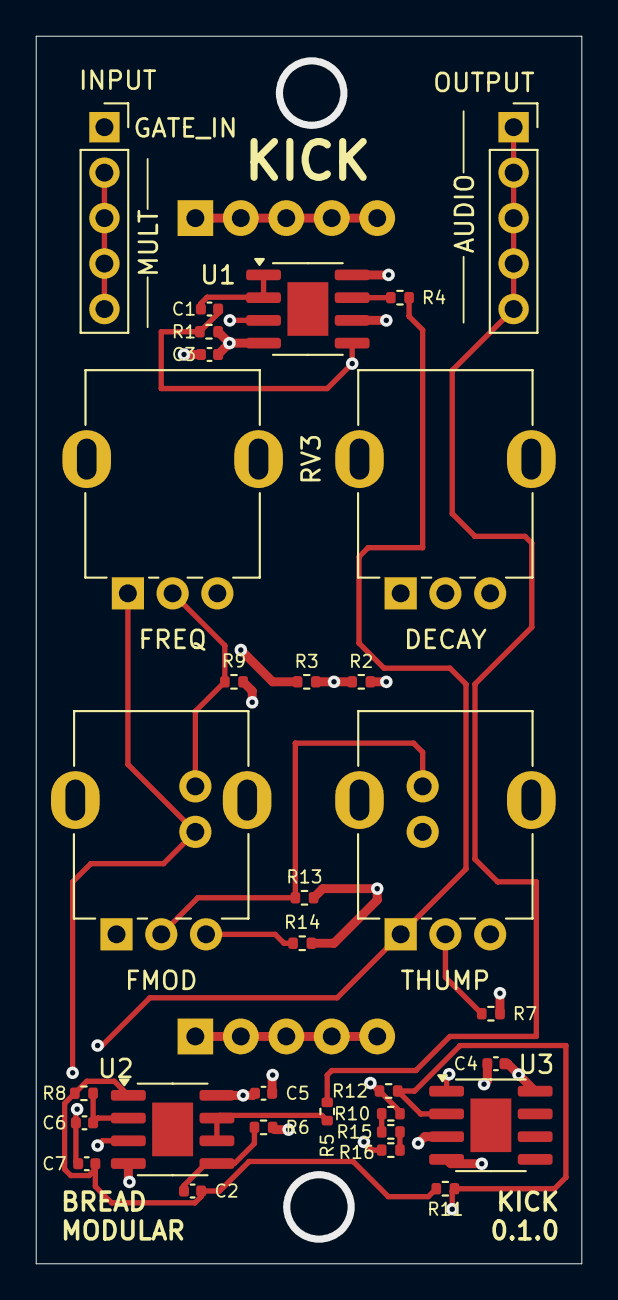
[picture p62: board kick.kicad_pcb from above]

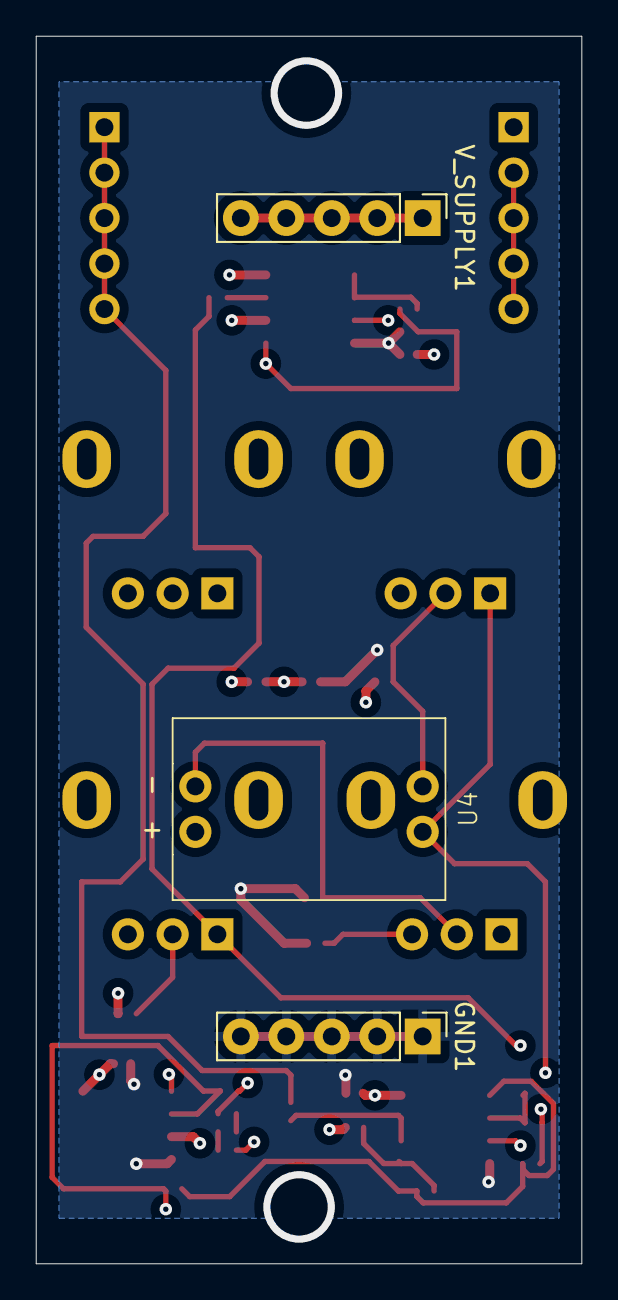
[picture p63: board kick.kicad_pcb from below]

Board: 4 copper layers, 30.5 x 68.6 mm, 35 parts (3 on the bottom side), 23 nets.
