tinkeringjoe/bread-modular/modules/line_in/line_in.kicad_pcb

## KiCad design modules/line_in/line_in.kicad_pcb (2024-11-17)

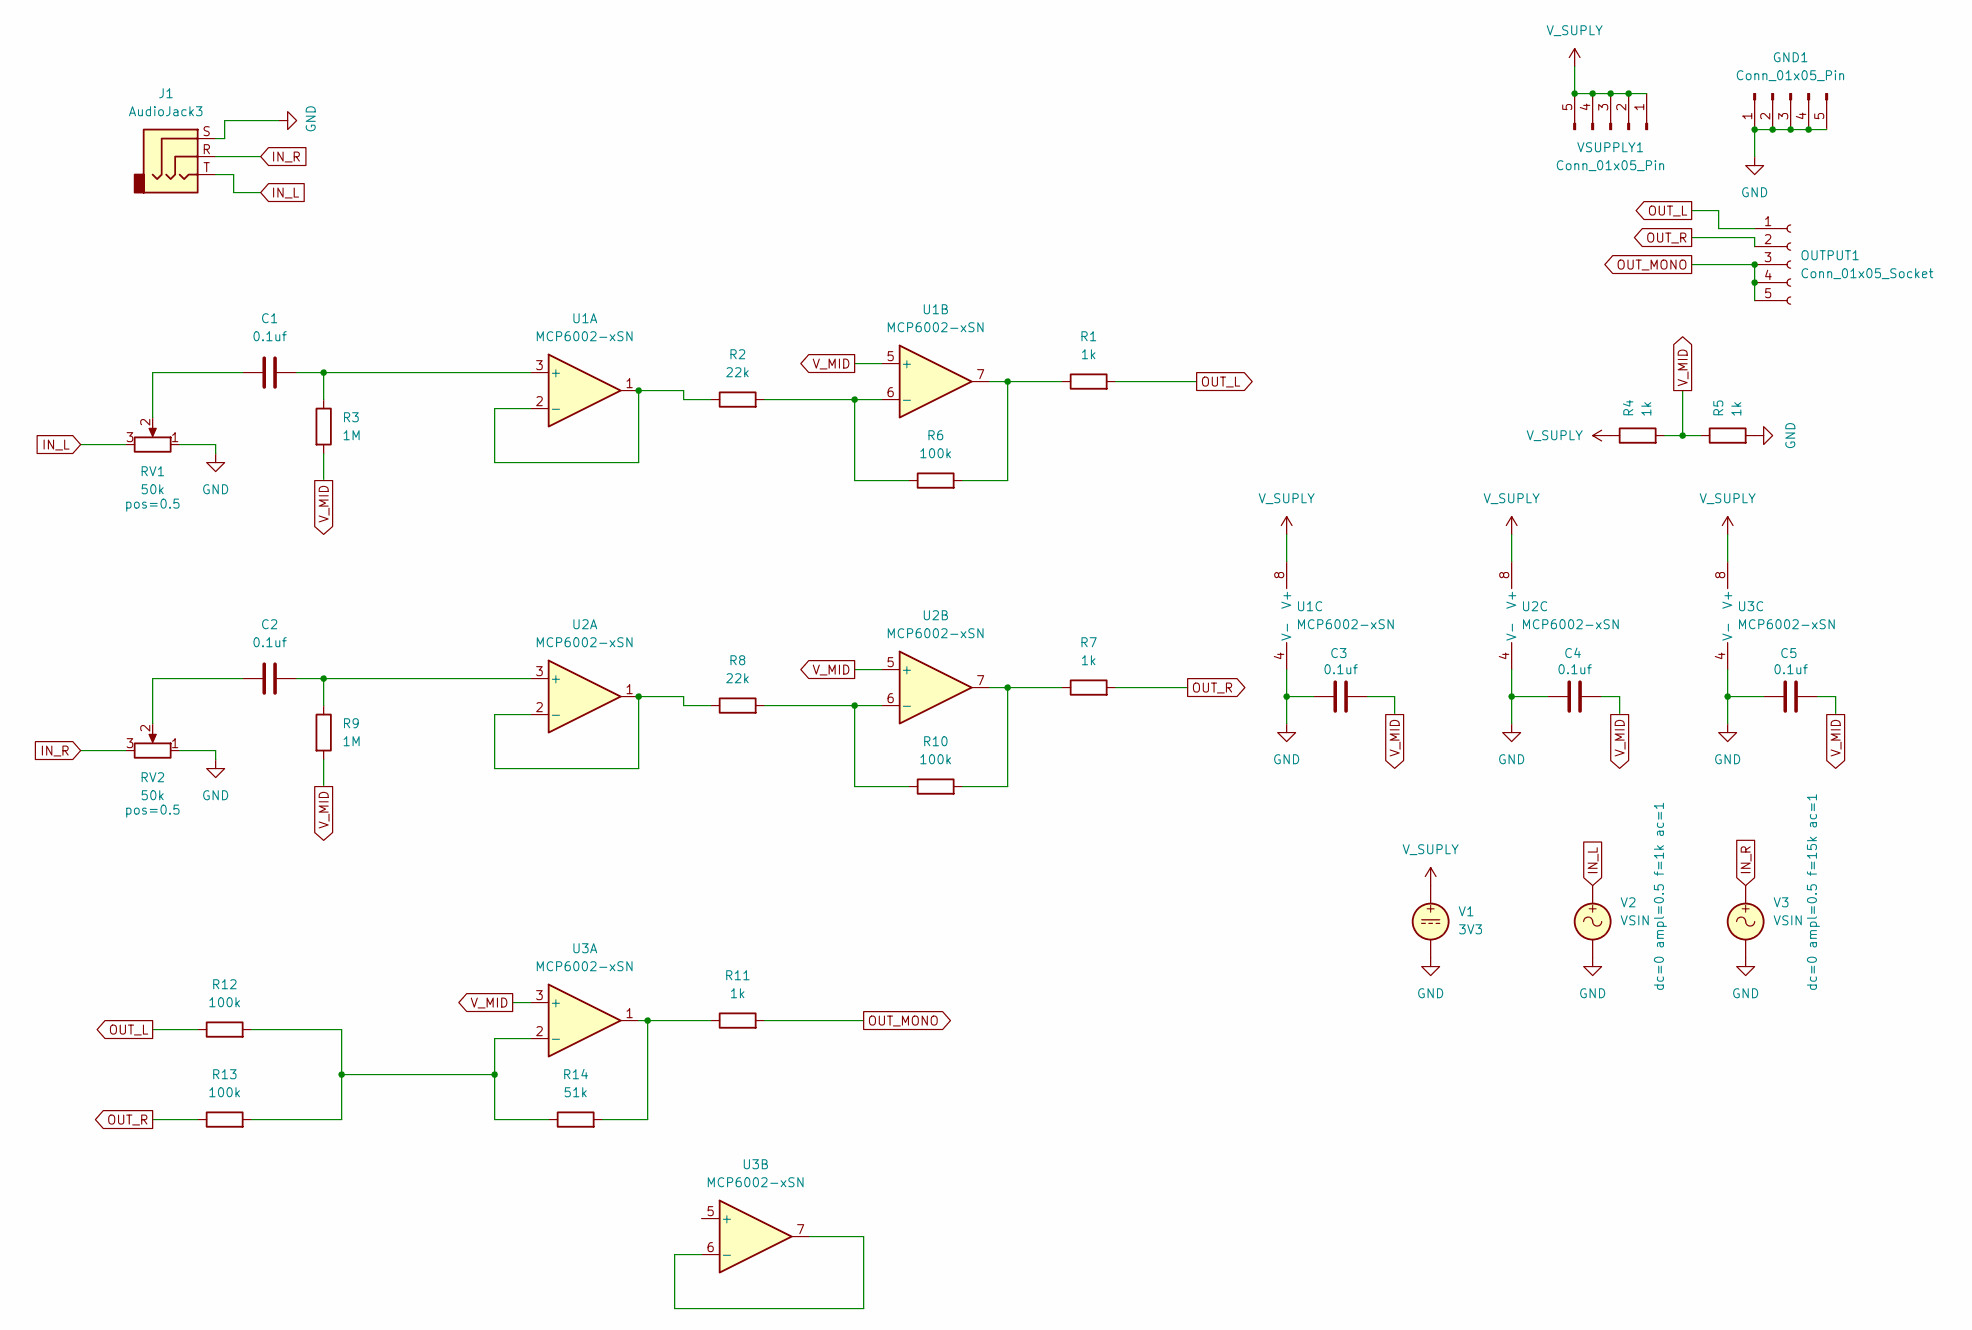
[picture p64: schematic line_in.kicad_sch]

Parts:
C1, C2, C3, C4, C5: 0.1uf; C_0402_1005Metric
GND1: Conn_01x05_Pin; Power_Connector
J1: AudioJack3; Jack_3.5mm_QingPu_WQP-PJ366ST_Vertical
OUTPUT1: Conn_01x05_Socket; PinSocket_1x05_P2.54mm_Vertical
R1, R4, R5, R7, R11: 1k; R_0402_1005Metric
R2, R8: 22k; R_0402_1005Metric
R3, R9: 1M; R_0402_1005Metric
R6, R10, R12, R13: 100k; R_0402_1005Metric
R14: 51k; R_0402_1005Metric
RV1, RV2: 50k; Potentiometer_RV09
U1, U2, U3: MCP6002-xSN; SOIC-8-1EP_3.9x4.9mm_P1.27mm_EP2.29x3mm
V1: 3V3
V2, V3: VSIN
VSUPPLY1: Conn_01x05_Pin; Power_Connector

Connections:
GND: C3.1, C4.1, C5.1, GND1.1, GND1.2, GND1.3, GND1.4, GND1.5, J1.S, R5.2, RV1.1, RV2.1, U1.4 (V-), U2.4 (V-), U3.4 (V-), V1.2, V2.2, V3.2
IN_L: J1.T, RV1.3, V2.1
IN_R: J1.R, RV2.3, V3.1
unnamed: C1.1, RV1.2
unnamed: C2.1, RV2.2
unnamed: R1.1, R6.2, U1.7
unnamed: R7.1, R10.2, U2.7
unnamed: R11.1, R14.2, U3.1
unnamed: C1.2, R3.1, U1.3 (+)
unnamed: R2.1, U1.1, U1.2 (-)
unnamed: R2.2, R6.1, U1.6 (-)
unnamed: C2.2, R9.1, U2.3 (+)
unnamed: R8.1, U2.1, U2.2 (-)
unnamed: R8.2, R10.1, U2.6 (-)
unnamed: R12.2, R13.2, R14.1, U3.2 (-)
unnamed: U3.6 (-), U3.7
OUT_L: OUTPUT1.1, R1.2, R12.1
OUT_MONO: OUTPUT1.3, OUTPUT1.4, OUTPUT1.5, R11.2
OUT_R: OUTPUT1.2, R7.2, R13.1
V_MID: C3.2, C4.2, C5.2, R3.2, R4.2, R5.1, R9.2, U1.5 (+), U2.5 (+), U3.3 (+)
V_SUPLY: R4.1, U1.8 (V+), U2.8 (V+), U3.8 (V+), V1.1, VSUPPLY1.1, VSUPPLY1.2, VSUPPLY1.3, VSUPPLY1.4, VSUPPLY1.5
