tinkeringjoe/bread-modular/modules/line_in/line_in.kicad_pcb

## KiCad design modules/line_in/line_in.kicad_pcb (continued)

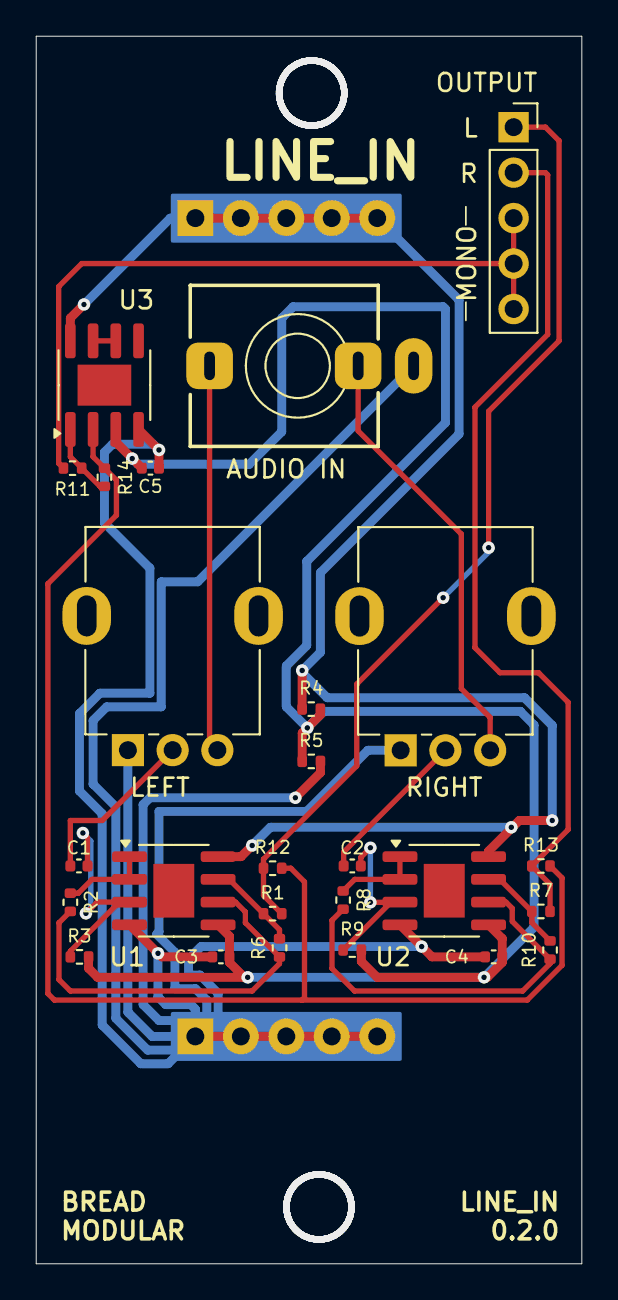
[picture p65: board line_in.kicad_pcb from above]

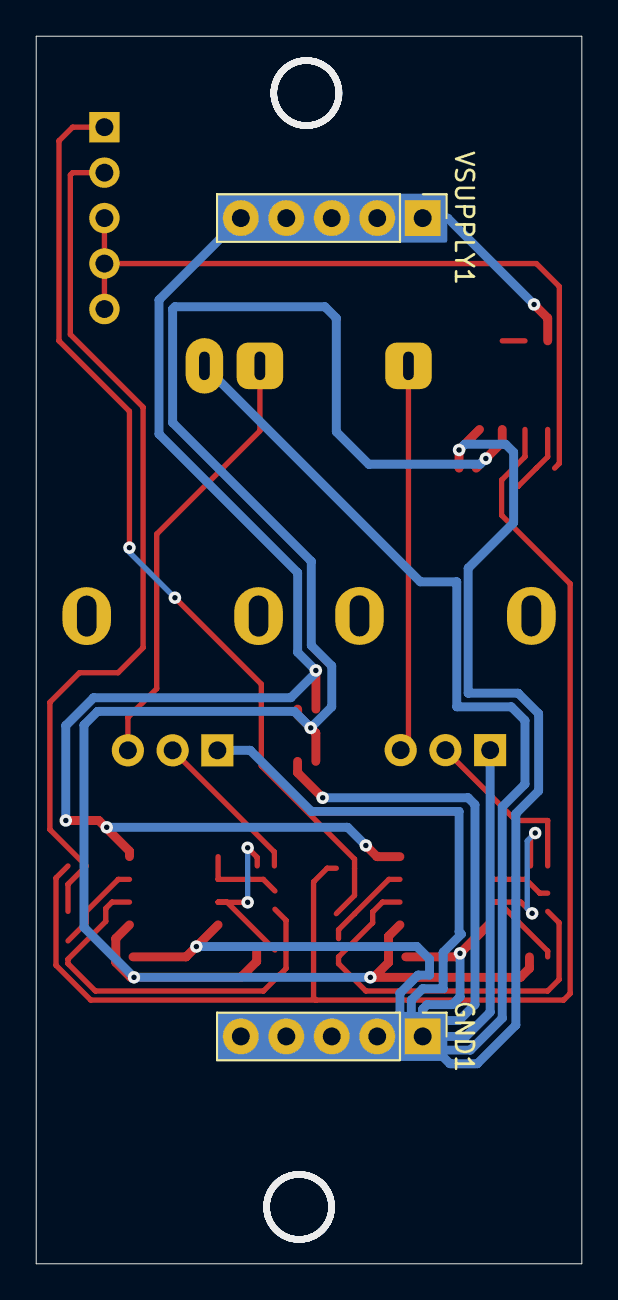
[picture p66: board line_in.kicad_pcb from below]

Board: 2 copper layers, 30.5 x 68.6 mm, 28 parts (2 on the bottom side), 21 nets.
