tinkeringjoe/bread-modular/modules/v2ca/v2ca.kicad_pcb

## KiCad design modules/v2ca/v2ca.kicad_pcb (2024-11-14)

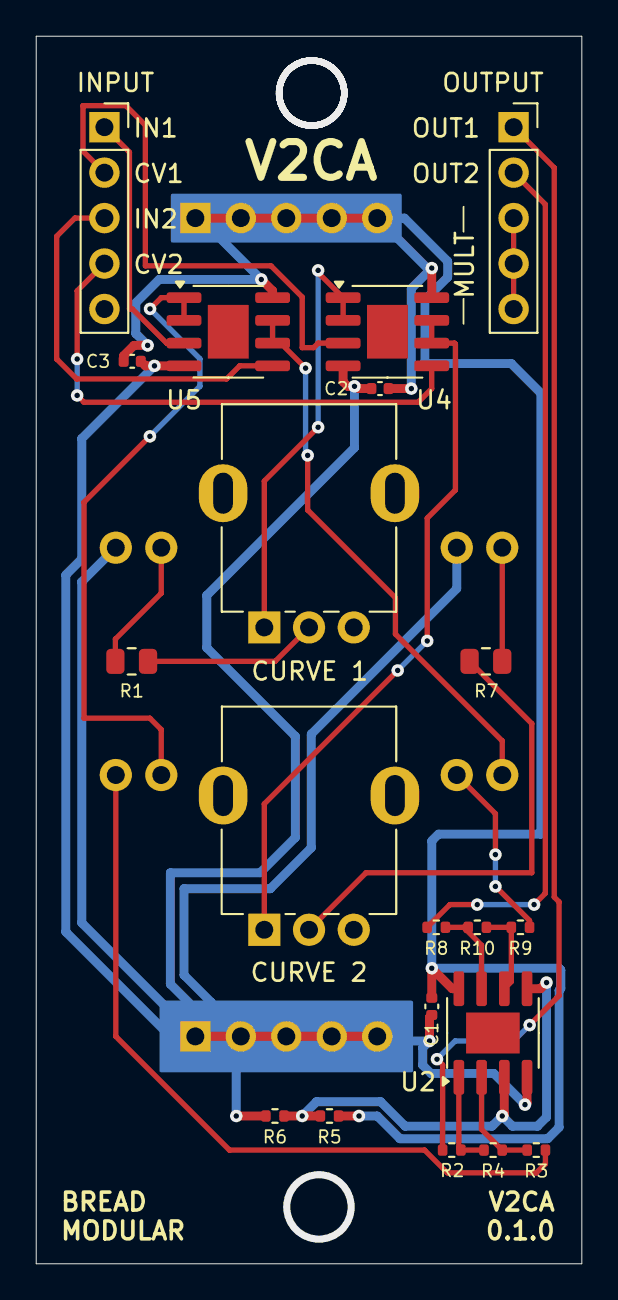
[picture p67: board v2ca.kicad_pcb from above]

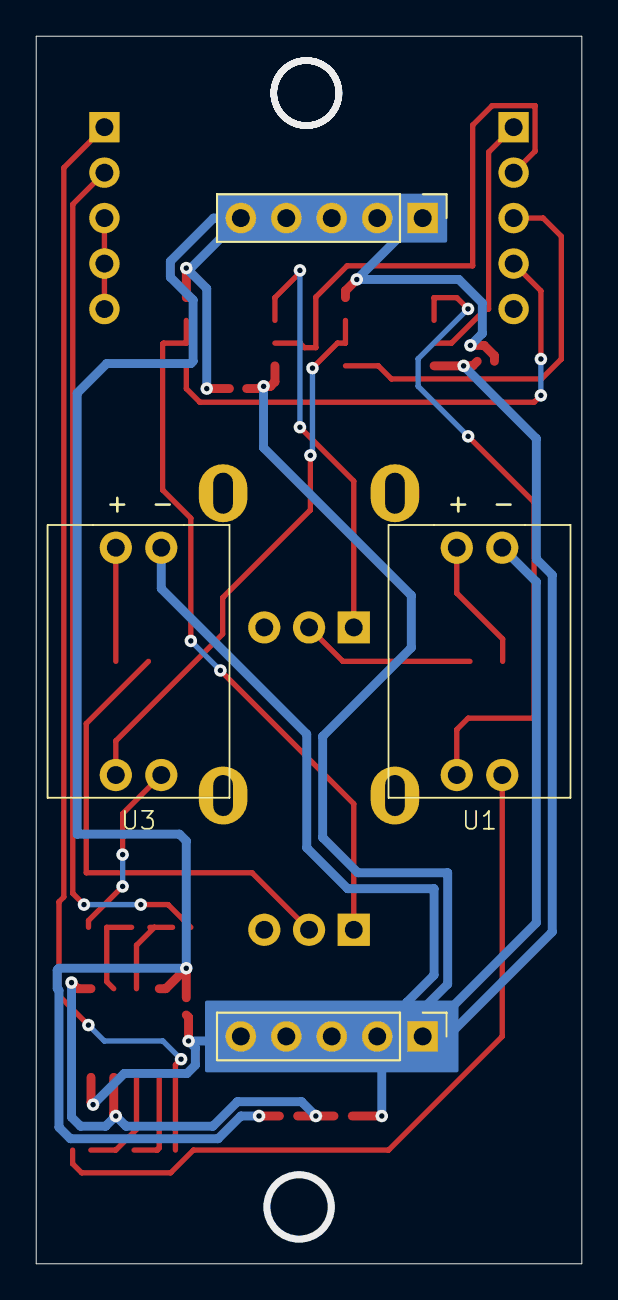
[picture p68: board v2ca.kicad_pcb from below]

Board: 2 copper layers, 30.5 x 68.6 mm, 24 parts (4 on the bottom side), 24 nets.

Parts:
5V1: Conn_01x05_Pin; PinHeader_1x05_P2.54mm_Vertical
C1, C2, C3: 0.1uf; C_0402_1005Metric
GND1: Conn_01x05_Pin; PinHeader_1x05_P2.54mm_Vertical
INPUT1: Conn_01x05_Socket; PinSocket_1x05_P2.54mm_Vertical
OUTPUT1: Conn_01x05_Socket; PinSocket_1x05_P2.54mm_Vertical
R1, R7: 330; R_0805_2012Metric
R2, R5, R6, R8: 1k; R_0402_1005Metric
R3, R4, R9, R10: 10k; R_0402_1005Metric
RV1, RV2: 50k; Potentiometer_RV09
U1, U3: VTL5C
U2, U4, U5: MCP6002-xSN; SOIC-8-1EP_3.9x4.9mm_P1.27mm_EP2.29x3mm

Connections:
+2.5V: R5.2, R6.1, U2.3 (+), U2.5 (+)
+5V: 5V1.1, 5V1.2, 5V1.3, 5V1.4, 5V1.5, C1.1, C2.1, C3.1, R5.1, U2.8 (V+), U4.8 (V+), U5.8 (V+)
CV1_IN: INPUT1.2, U4.3 (+)
CV2_IN: INPUT1.4, U4.5 (+)
GND: C1.2, C2.2, C3.2, GND1.1, GND1.2, GND1.3, GND1.4, GND1.5, R6.2, U1.1 (-), U2.4 (V-), U3.1 (-), U4.4 (V-), U5.4 (V-)
unnamed: OUTPUT1.3, OUTPUT1.4, OUTPUT1.5
unnamed: R1.1, RV1.2
unnamed: R2.1, R4.2, U2.1
unnamed: R3.1, U1.3
unnamed: R7.1, RV2.2
unnamed: R9.1, U3.3
unnamed: R8.1, R10.2, U2.7
unnamed: R1.2, U1.2 (+)
unnamed: R3.2, R4.1, U2.2 (-)
unnamed: R9.2, R10.1, U2.6 (-)
unnamed: R7.2, U3.2 (+)
unnamed: RV1.1, U4.1, U4.2 (-)
unnamed: RV2.1, U4.6 (-), U4.7
unnamed: U1.4, U5.1, U5.2 (-)
unnamed: U3.4, U5.6 (-), U5.7
V1_IN: INPUT1.1, U5.3 (+)
V1_OUT: OUTPUT1.1, R2.2
V2_IN: INPUT1.3, U5.5 (+)
V2_OUT: OUTPUT1.2, R8.2
