tinkeringjoe/bread-modular/modules/wave/wave.kicad_pcb

## KiCad design modules/wave/wave.kicad_pcb (2024-11-05)

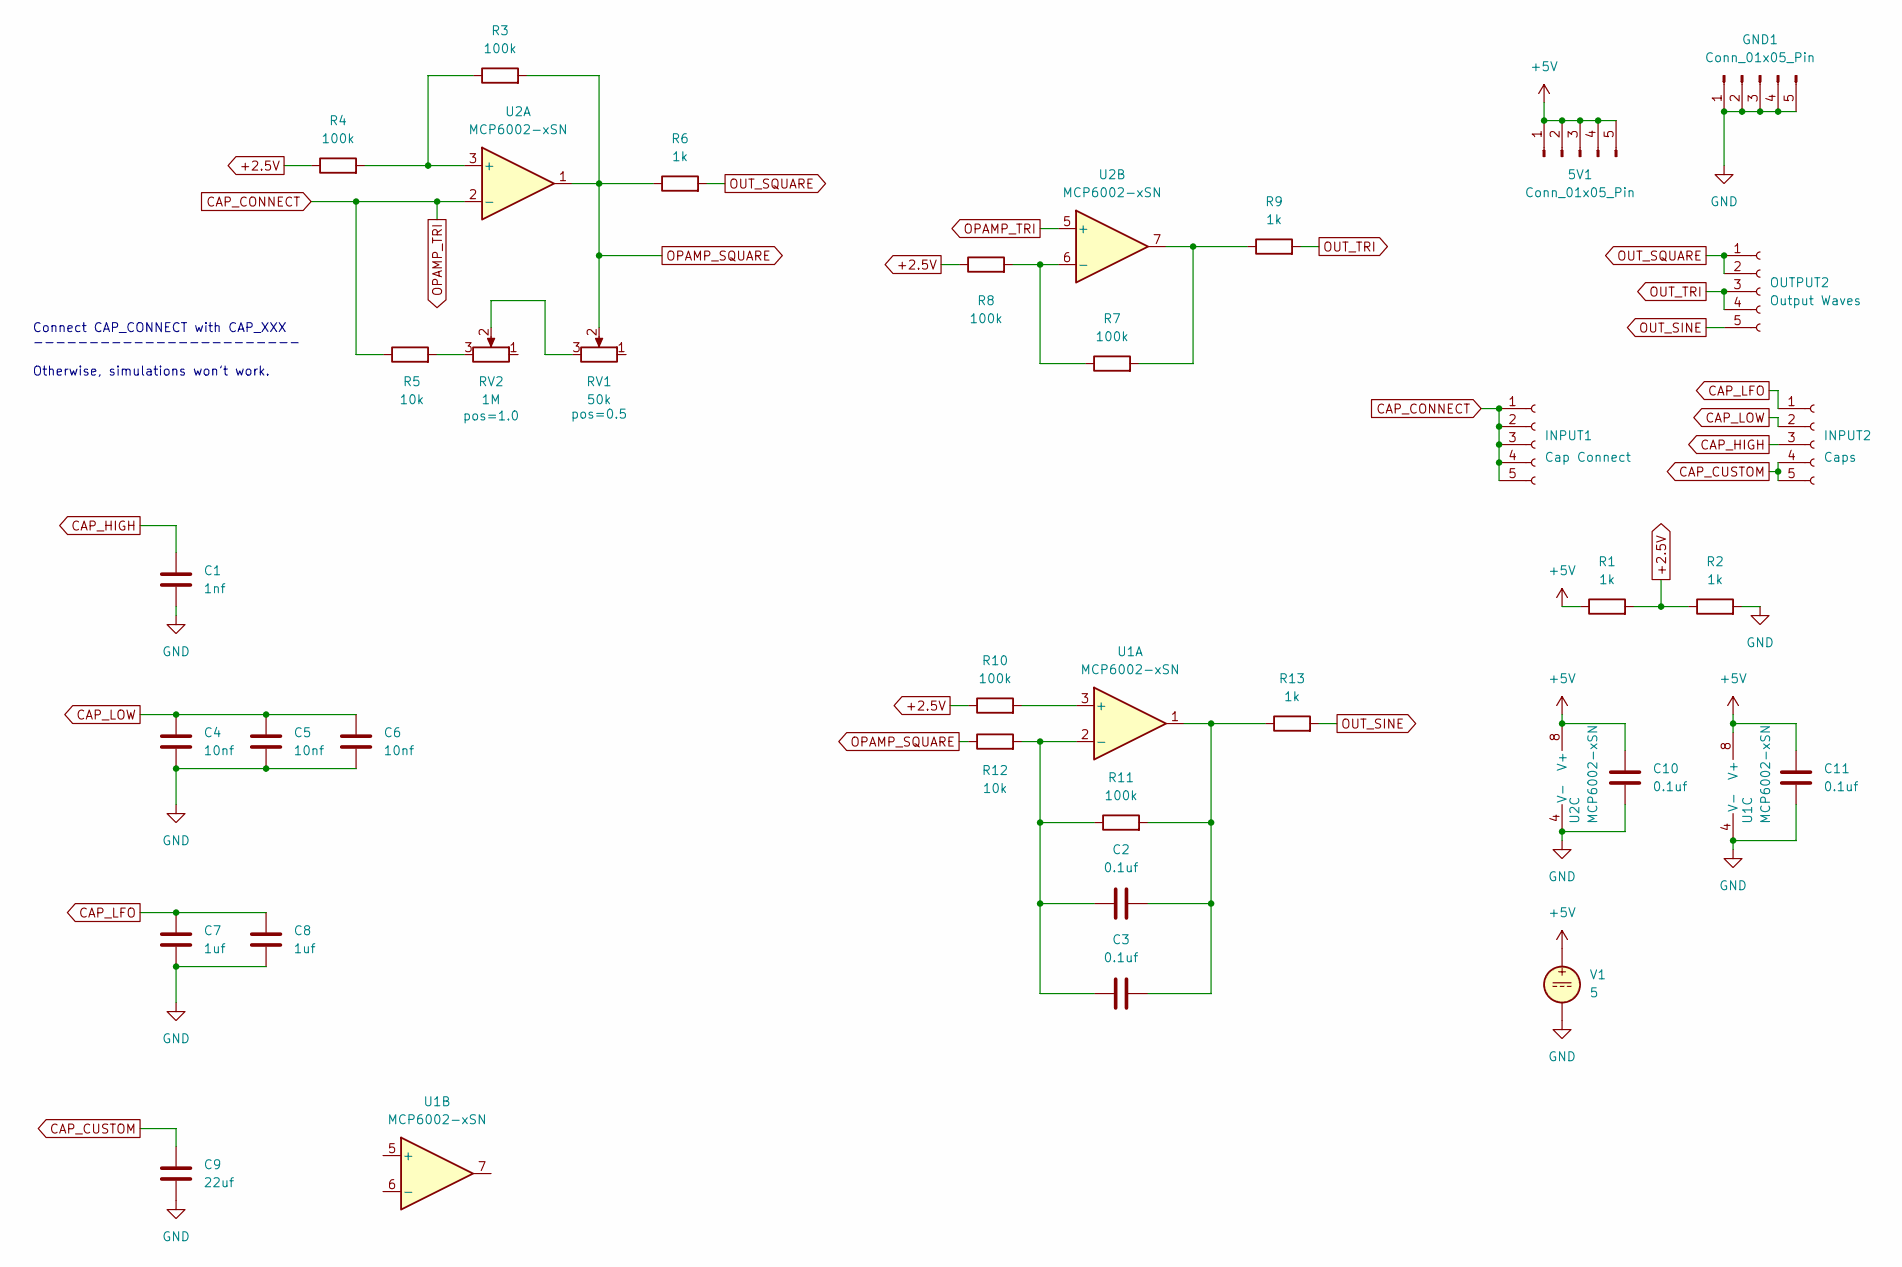
[picture p69: schematic wave.kicad_sch]

Parts:
5V1: Conn_01x05_Pin; PinHeader_1x05_P2.54mm_Vertical
C1: 1nf; C_0402_1005Metric
C2, C3, C10, C11: 0.1uf; C_0402_1005Metric
C4, C5, C6: 10nf; C_0402_1005Metric
C7, C8: 1uf; C_0402_1005Metric
C9: 22uf; C_0805_2012Metric
GND1: Conn_01x05_Pin; PinHeader_1x05_P2.54mm_Vertical
INPUT1: Cap Connect; PinSocket_1x05_P2.54mm_Vertical
INPUT2: Caps; PinSocket_1x05_P2.54mm_Vertical
OUTPUT2: Output Waves; PinSocket_1x05_P2.54mm_Vertical
R1, R2, R6, R9, R13: 1k; R_0402_1005Metric
R3, R4, R7, R8, R10, R11: 100k; R_0402_1005Metric
R5, R12: 10k; R_0402_1005Metric
RV1: 50k; Potentiometer_RV09
RV2: 1M; Potentiometer_RV09
U1, U2: MCP6002-xSN; SOIC-8-1EP_3.9x4.9mm_P1.27mm_EP2.29x3mm
V1: 5

Connections:
+2.5V: R1.2, R2.1, R4.1, R8.1, R10.1
+5V: 5V1.1, 5V1.2, 5V1.3, 5V1.4, 5V1.5, C10.1, C11.1, R1.1, U1.8 (V+), U2.8 (V+), V1.1
CAP_CONNECT: INPUT1.1, INPUT1.2, INPUT1.3, INPUT1.4, INPUT1.5, R5.1, U2.2 (-), U2.5 (+)
CAP_CUSTOM: C9.1, INPUT2.4, INPUT2.5
CAP_HIGH: C1.1, INPUT2.3
CAP_LFO: C7.1, C8.1, INPUT2.1
CAP_LOW: C4.1, C5.1, C6.1, INPUT2.2
GND: C1.2, C4.2, C5.2, C6.2, C7.2, C8.2, C9.2, C10.2, C11.2, GND1.1, GND1.2, GND1.3, GND1.4, GND1.5, R2.2, U1.4 (V-), U2.4 (V-), V1.2
unnamed: C2.2, C3.2, R11.2, R13.1, U1.1
unnamed: R5.2, RV2.3
unnamed: R7.2, R9.1, U2.7
unnamed: RV1.3, RV2.2
unnamed: R10.2, U1.3 (+)
unnamed: C2.1, C3.1, R11.1, R12.2, U1.2 (-)
unnamed: R3.1, R4.2, U2.3 (+)
unnamed: R7.1, R8.2, U2.6 (-)
OPAMP_SQUARE: R3.2, R6.1, R12.1, RV1.2, U2.1
OUT_SINE: OUTPUT2.5, R13.2
OUT_SQUARE: OUTPUT2.1, OUTPUT2.2, R6.2
OUT_TRI: OUTPUT2.3, OUTPUT2.4, R9.2

Notes on the sheet:
Connect CAP_CONNECT with CAP_XXX ------------------------ Otherwise, simulations won't work.

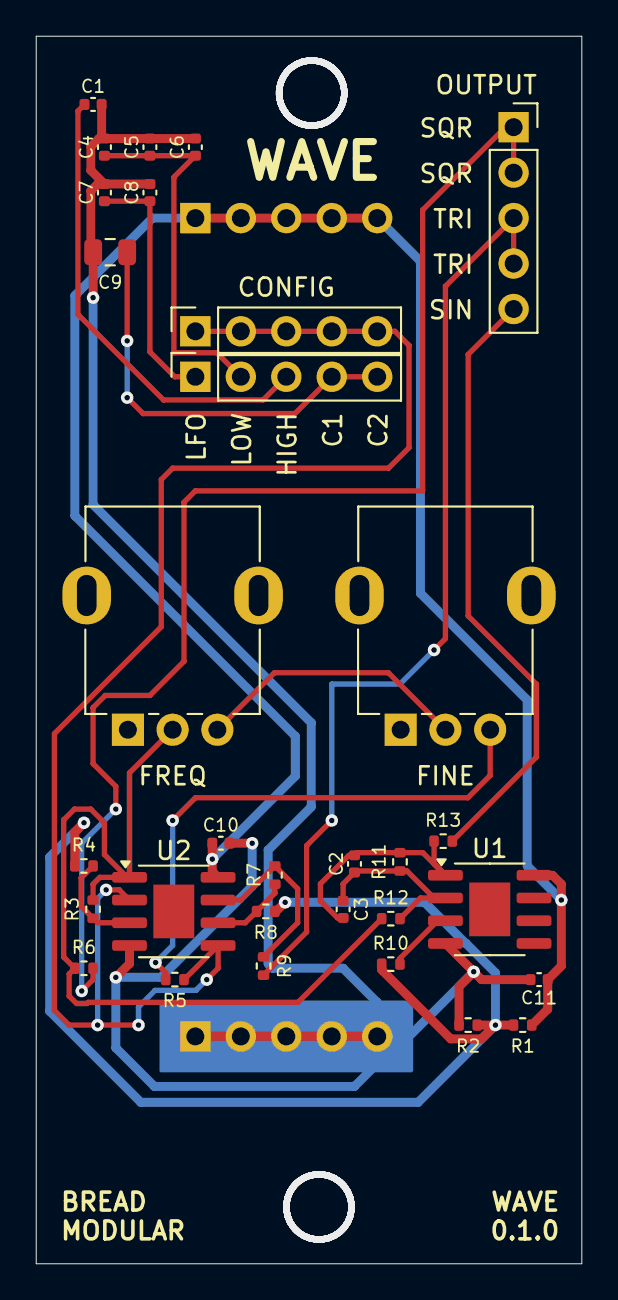
[picture p70: board wave.kicad_pcb from above]

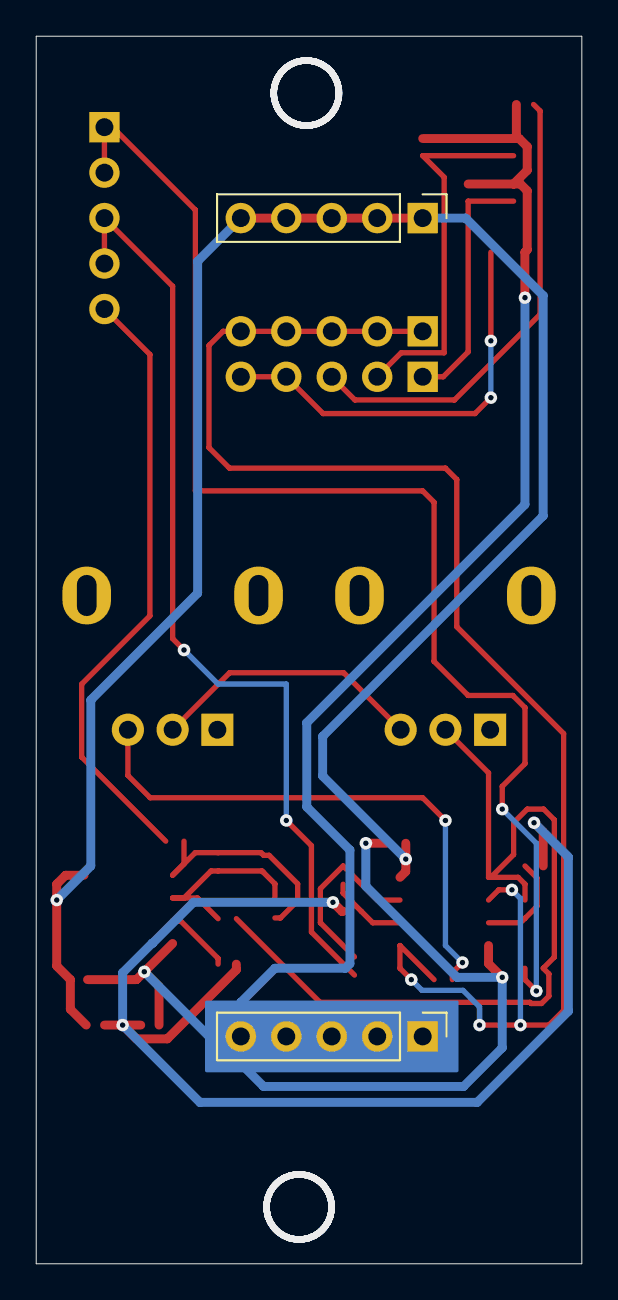
[picture p71: board wave.kicad_pcb from below]

Board: 2 copper layers, 30.5 x 68.6 mm, 33 parts (2 on the bottom side), 20 nets.
