tinkeringjoe/bread-modular/modules/ar_env/ar_env.kicad_pcb

## KiCad design modules/ar_env/ar_env.kicad_pcb (2024-11-04)

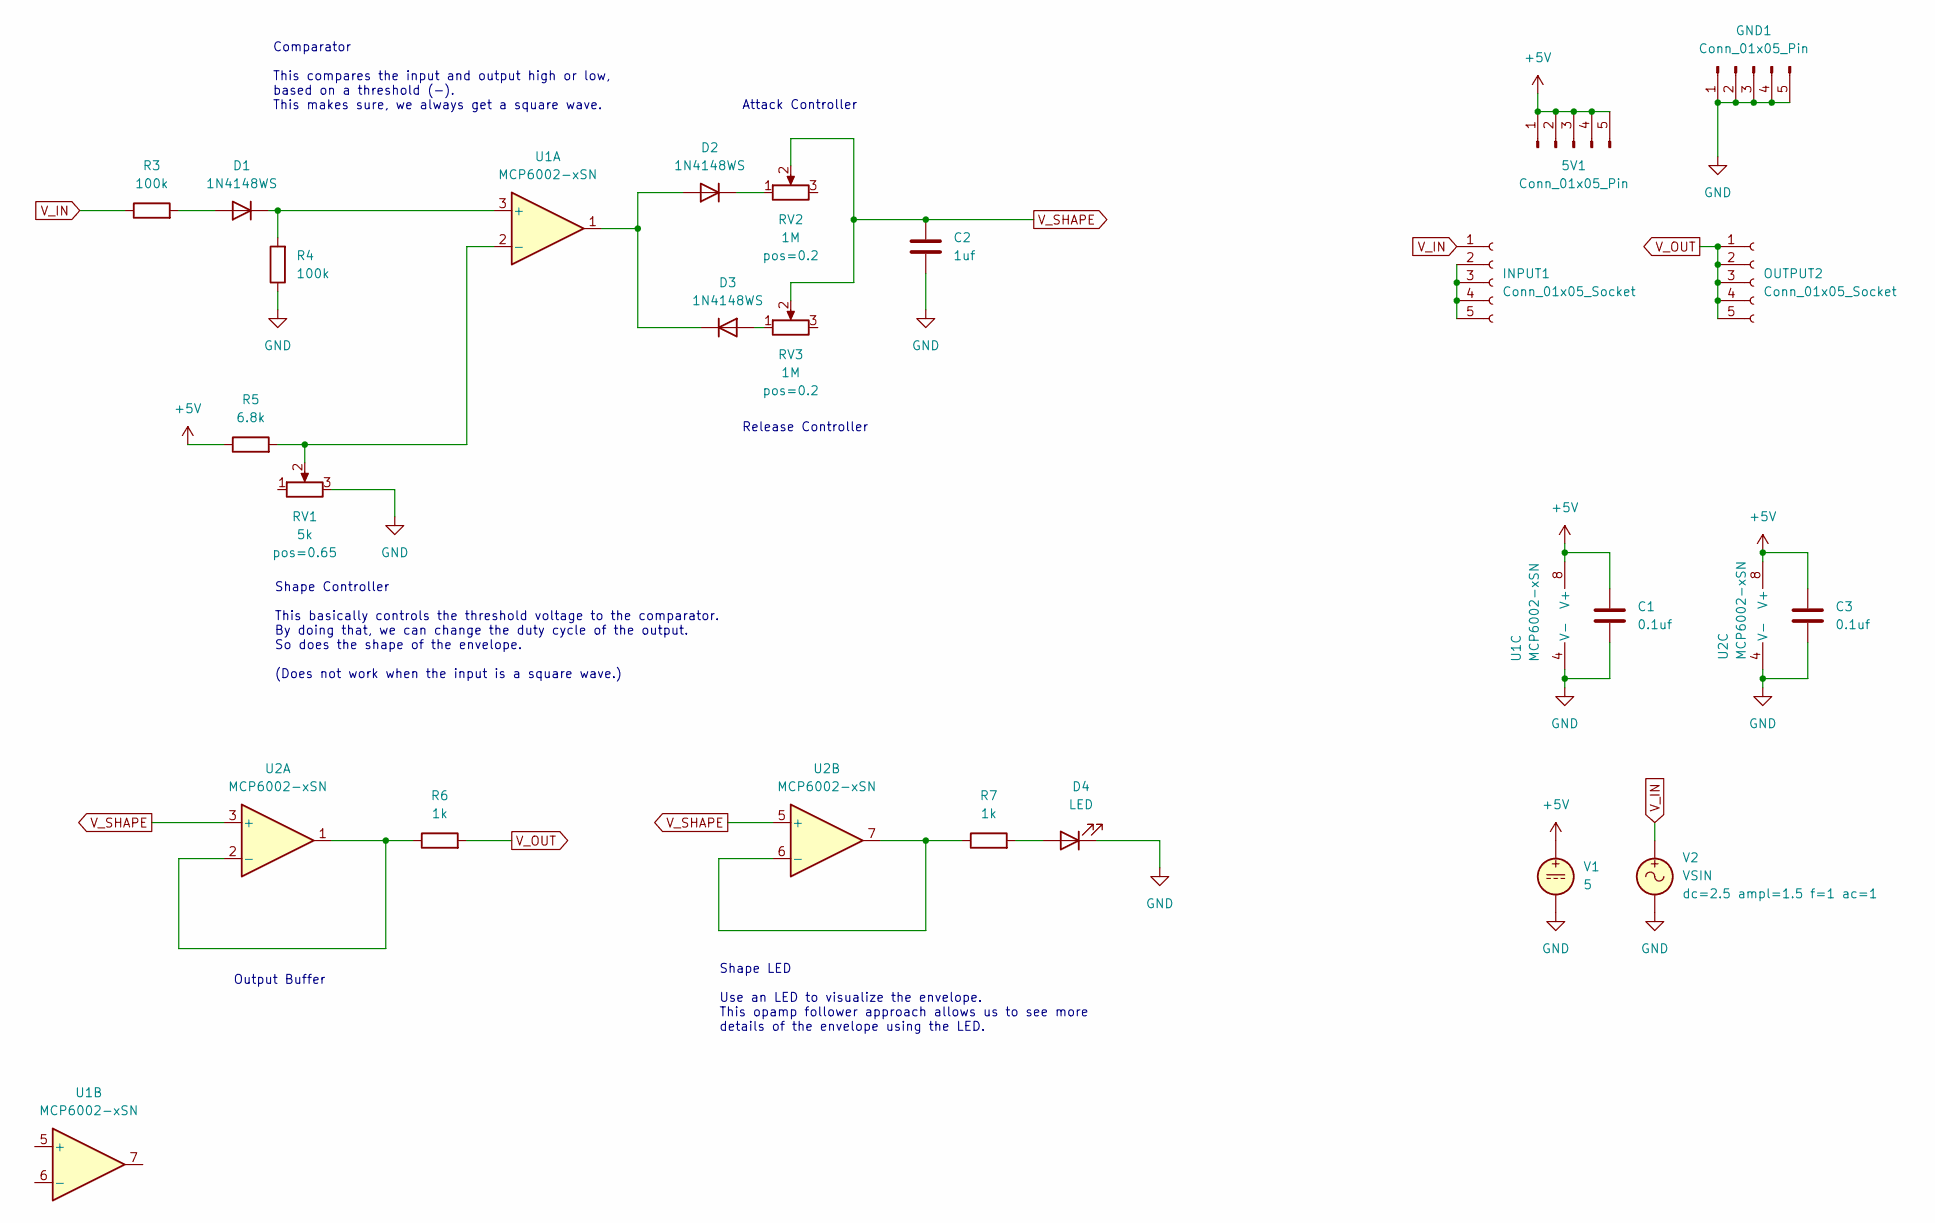
[picture p72: schematic ar_env.kicad_sch]

Parts:
5V1: Conn_01x05_Pin; PinHeader_1x05_P2.54mm_Vertical
C1, C3: 0.1uf; C_0402_1005Metric
C2: 1uf; C_1206_3216Metric
D1, D2, D3: 1N4148WS; D_SOD-323_HandSoldering
D4: LED; LED_0603_1608Metric
GND1: Conn_01x05_Pin; PinHeader_1x05_P2.54mm_Vertical
INPUT1: Conn_01x05_Socket; PinSocket_1x05_P2.54mm_Vertical
OUTPUT2: Conn_01x05_Socket; PinSocket_1x05_P2.54mm_Vertical
R3, R4: 100k; R_0402_1005Metric
R5: 6.8k; R_0603_1608Metric
R6, R7: 1k; R_0402_1005Metric
RV1: 5k; Potentiometer_RV09
RV2, RV3: 1M; Potentiometer_RV09
U1, U2: MCP6002-xSN; SOIC-8-1EP_3.9x4.9mm_P1.27mm_EP2.29x3mm
V1: 5
V2: VSIN

Connections:
+5V: 5V1.1, 5V1.2, 5V1.3, 5V1.4, 5V1.5, C1.1, C3.1, R5.1, U1.8 (V+), U2.8 (V+), V1.1
GND: C1.2, C2.2, C3.2, D4.1 (K), GND1.1, GND1.2, GND1.3, GND1.4, GND1.5, R4.1, RV1.3, U1.4 (V-), U2.4 (V-), V1.2, V2.2
unnamed: D1.2 (A), R3.2
unnamed: D1.1 (K), R4.2, U1.3 (+)
unnamed: D2.2 (A), D3.1 (K), U1.1
unnamed: D2.1 (K), RV2.1
unnamed: D3.2 (A), RV3.1
unnamed: D4.2 (A), R7.2
unnamed: INPUT1.2, INPUT1.3, INPUT1.4, INPUT1.5
unnamed: R5.2, RV1.2, U1.2 (-)
unnamed: R6.1, U2.1, U2.2 (-)
unnamed: R7.1, U2.6 (-), U2.7
V_IN: INPUT1.1, R3.1, V2.1
V_OUT: OUTPUT2.1, OUTPUT2.2, OUTPUT2.3, OUTPUT2.4, OUTPUT2.5, R6.2
V_SHAPE: C2.1, RV2.2, RV3.2, U2.3 (+), U2.5 (+)

Notes on the sheet:
Shape LED Use an LED to visualize the envelope. This opamp follower approach allows us to see more details of the envelope using the LED.
Shape Controller This basically controls the threshold voltage to the comparator. By doing that, we can change the duty cycle of the output. So does the shape of the envelope. (Does not work when the input is a square wave.)
Release Controller
Output Buffer
Attack Controller
Comparator This compares the input and output high or low, based on a threshold (-). This makes sure, we always get a square wave.

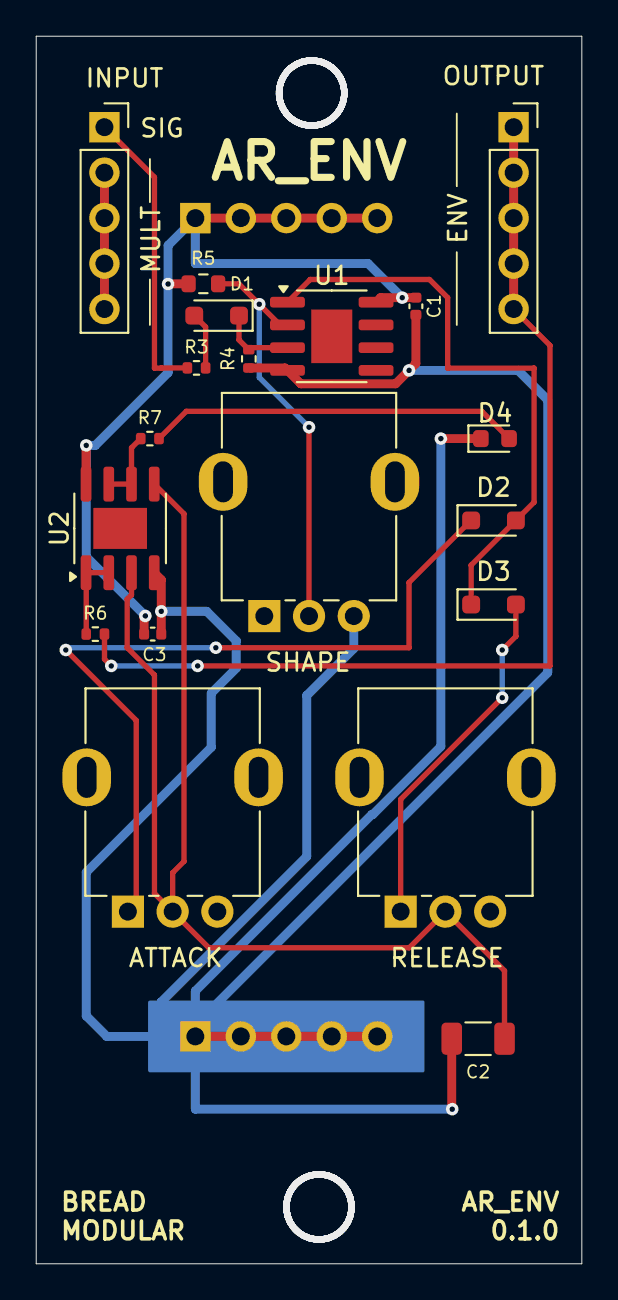
[picture p73: board ar_env.kicad_pcb from above]

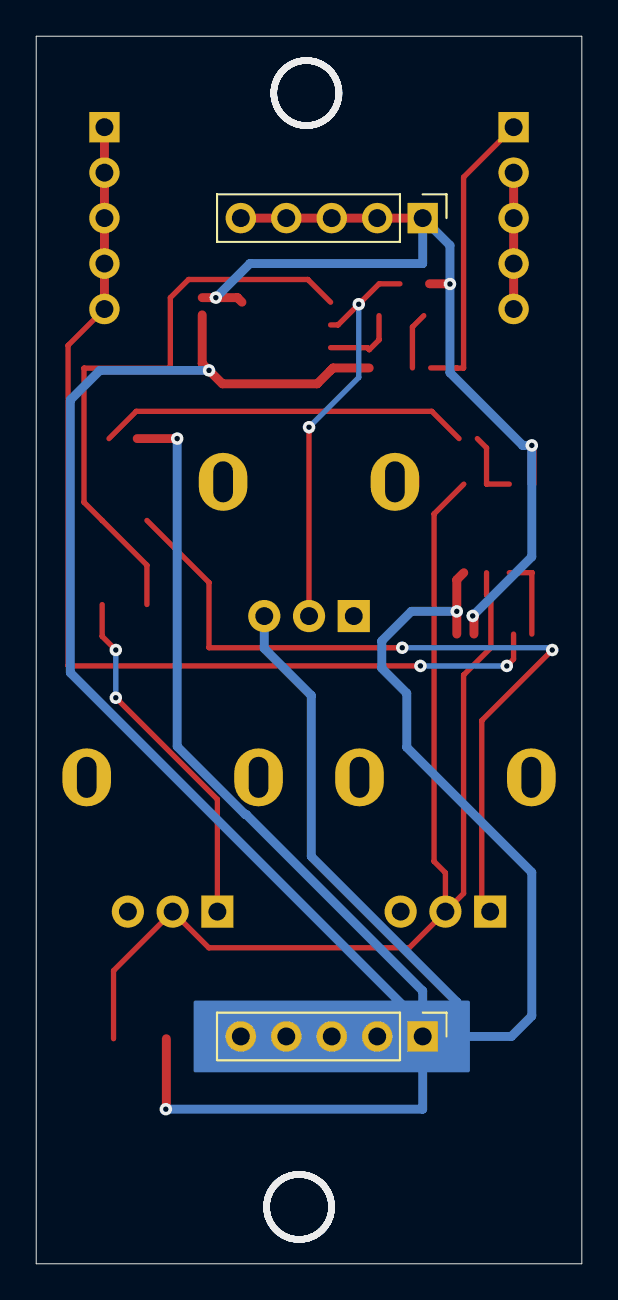
[picture p74: board ar_env.kicad_pcb from below]

Board: 2 copper layers, 30.5 x 68.6 mm, 21 parts (2 on the bottom side), 15 nets.
