tinkeringjoe/bread-modular/modules/rv_base/rv_base.kicad_pcb

## KiCad design modules/rv_base/rv_base.kicad_pcb (2024-11-01)

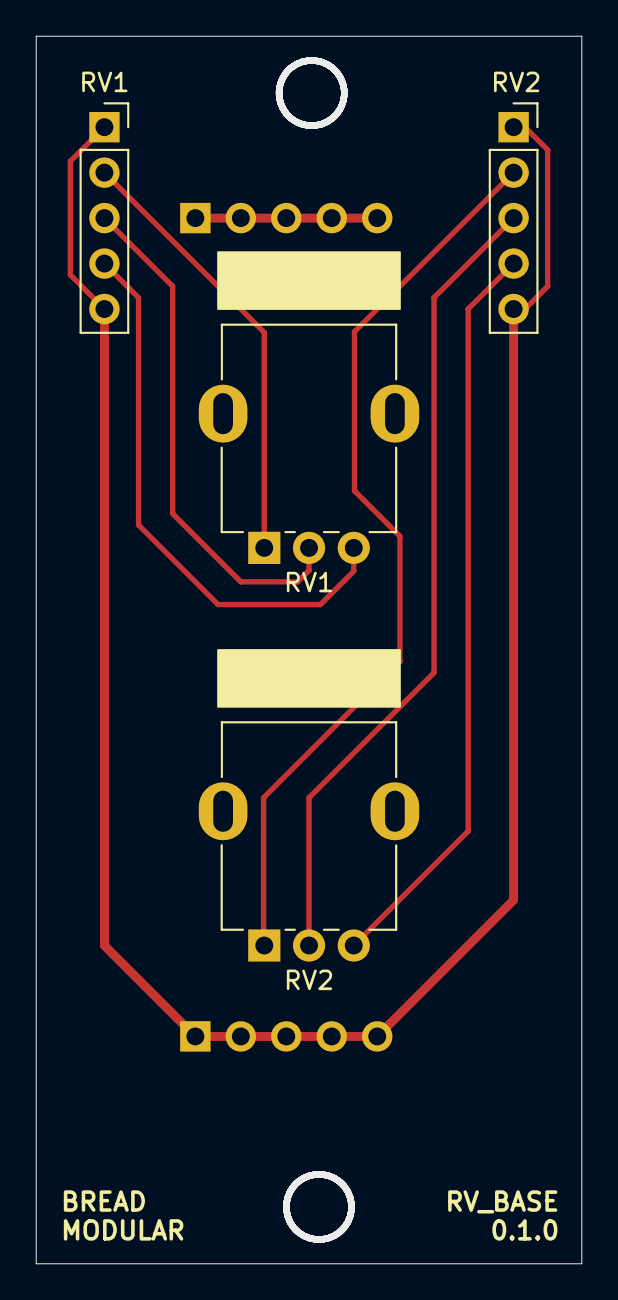
[picture p75: board rv_base.kicad_pcb from above]

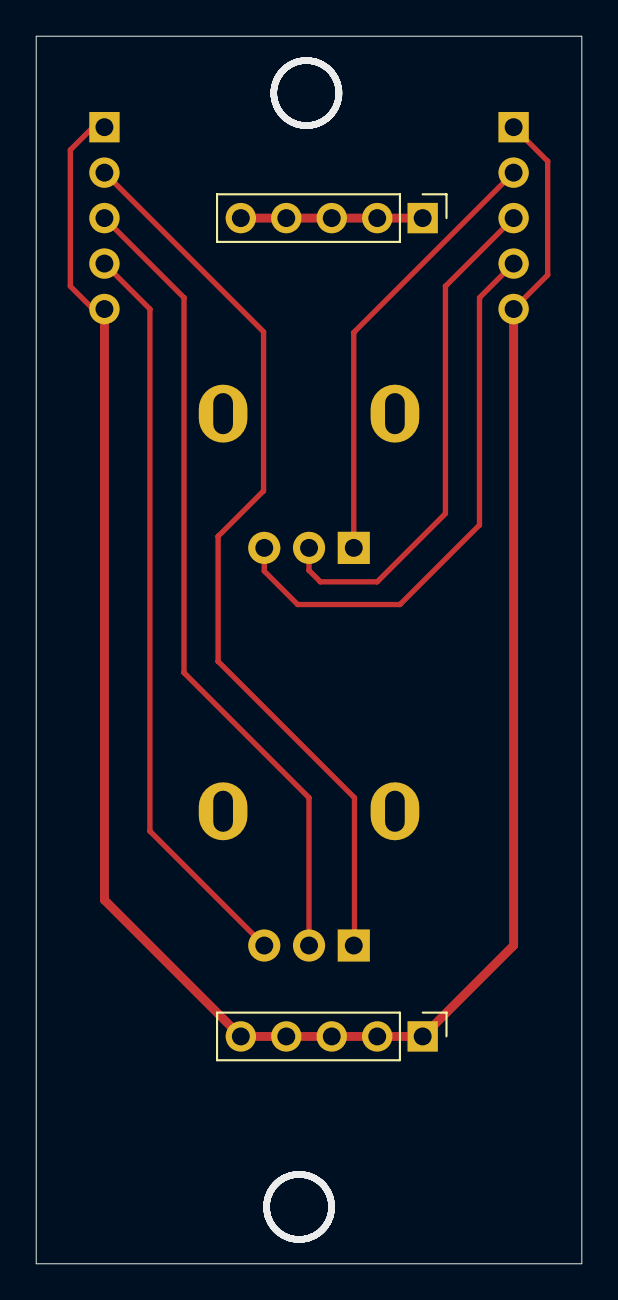
[picture p76: board rv_base.kicad_pcb from below]

Board: 2 copper layers, 30.5 x 68.6 mm, 6 parts (2 on the bottom side), 8 nets.

Parts:
5V1: Conn_01x05_Pin; PinHeader_1x05_P2.54mm_Vertical
GND1: Conn_01x05_Pin; PinHeader_1x05_P2.54mm_Vertical
INPUT1: Conn_01x05_Socket; PinSocket_1x05_P2.54mm_Vertical
OUTPUT2: Conn_01x05_Socket; PinSocket_1x05_P2.54mm_Vertical
RV1, RV2: R_Potentiometer; Potentiometer_RV09

Connections:
+5V: 5V1.1, 5V1.2, 5V1.3, 5V1.4, 5V1.5
GND: GND1.1, GND1.2, GND1.3, GND1.4, GND1.5, INPUT1.1, INPUT1.5, OUTPUT2.1, OUTPUT2.5
RV1_1: INPUT1.2, RV1.1
RV1_2: INPUT1.3, RV1.2
RV1_3: INPUT1.4, RV1.3
RV2_1: OUTPUT2.2, RV2.1
RV2_2: OUTPUT2.3, RV2.2
RV2_3: OUTPUT2.4, RV2.3
