tinkeringjoe/bread-modular/modules/jvca/jvca.kicad_pcb

## KiCad design modules/jvca/jvca.kicad_pcb (2024-10-29)

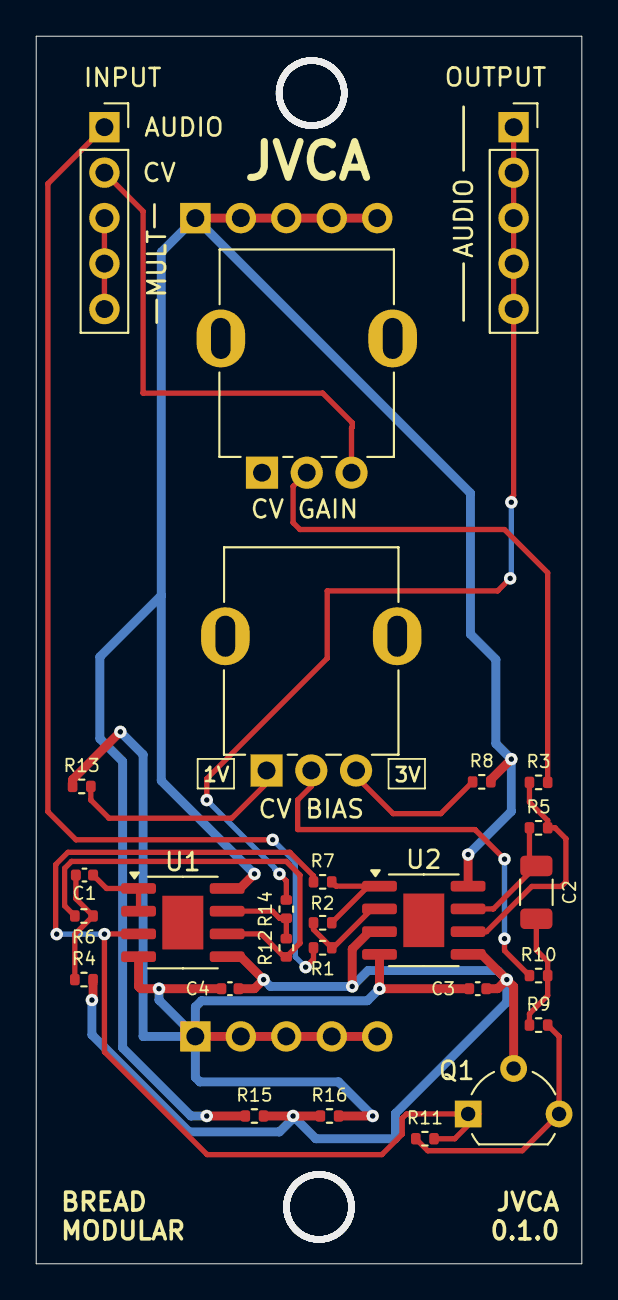
[picture p77: board jvca.kicad_pcb from above]

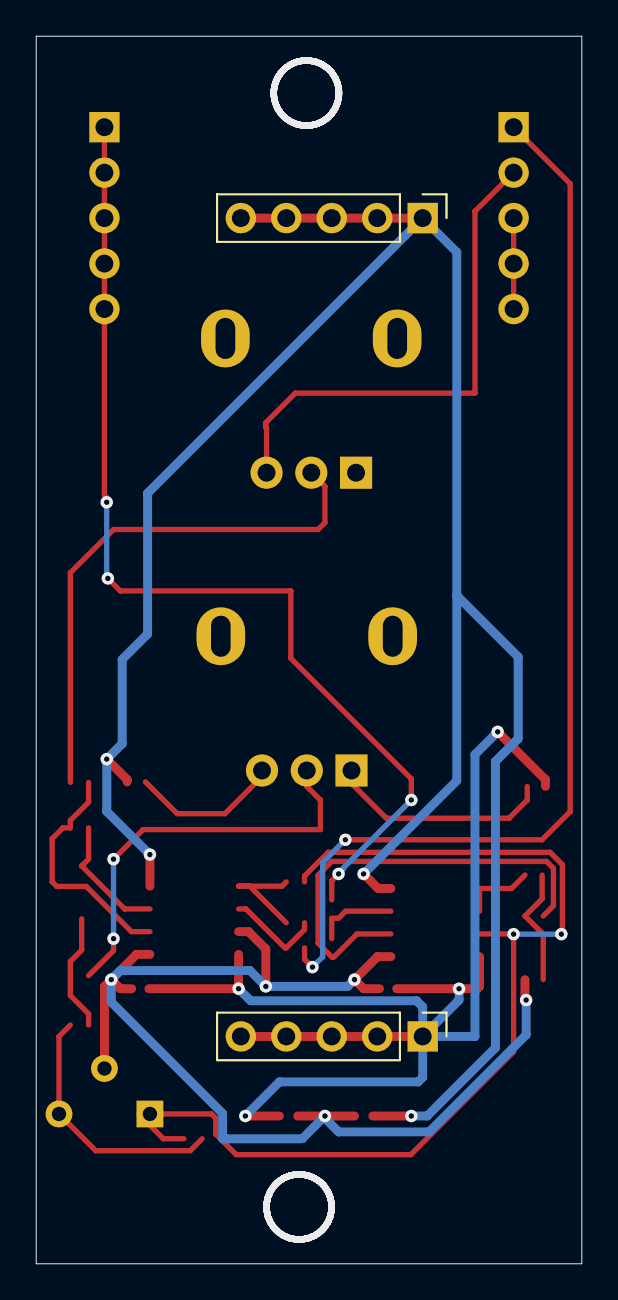
[picture p78: board jvca.kicad_pcb from below]

Board: 2 copper layers, 30.5 x 68.6 mm, 29 parts (2 on the bottom side), 22 nets.

Parts:
5V1: Conn_01x05_Pin; PinHeader_1x05_P2.54mm_Vertical
C1, C3, C4: 0.1uf; C_0402_1005Metric
C2: 4.7uf; C_1206_3216Metric
CV BIAS: 1k; Potentiometer_RV09
CV GAIN: 1M; Potentiometer_RV09
GND1: Conn_01x05_Pin; PinHeader_1x05_P2.54mm_Vertical
INPUT: Conn_01x05_Socket; PinSocket_1x05_P2.54mm_Vertical
OUTPUT: Conn_01x05_Socket; PinSocket_1x05_P2.54mm_Vertical
Q1: 2N5457; TO-92L_Wide
R1, R12: 200k; R_0402_1005Metric
R2, R6: 22k; R_0402_1005Metric
R3, R5: 51k; R_0402_1005Metric
R4, R7, R10: 100k; R_0402_1005Metric
R8: 2k; R_0402_1005Metric
R9, R11: 1M; R_0402_1005Metric
R13, R14, R15, R16: 1k; R_0402_1005Metric
U1, U2: MCP6002-xSN; SOIC-8-1EP_3.9x4.9mm_P1.27mm_EP2.29x3mm

Connections:
+2.5V: C3.2, C4.2, Q1.2 (S), R4.2, R15.2, R16.1, U1.5 (+), U2.3 (+), U2.5 (+)
+5V: 5V1.1, 5V1.2, 5V1.3, 5V1.4, 5V1.5, R8.2, R15.1, U1.8 (V+), U2.8 (V+)
CV: CV GAIN.3, INPUT.2
GND: C3.1, C4.1, GND1.1, GND1.2, GND1.3, GND1.4, GND1.5, R13.1, R16.2, U1.4 (V-), U2.4 (V-)
JFET_CV: C2.2, R9.1, R10.2
JFET_OUT: Q1.1 (D), R7.1, R11.2, U1.3 (+)
unnamed: C1.2, R4.1, R6.1
unnamed: C2.1, R5.1, U2.7
unnamed: INPUT.3, INPUT.4, INPUT.5
unnamed: Q1.3 (G), R9.2, R11.1
unnamed: R2.1, R7.2, U2.1
unnamed: CV GAIN.2, R3.2
unnamed: CV BIAS.3, R8.1
unnamed: CV BIAS.2, R10.1
unnamed: R12.2, R14.1, U1.7
unnamed: CV BIAS.1, R13.2
unnamed: C1.1, U1.1, U1.2 (-)
unnamed: R6.2, R12.1, U1.6 (-)
unnamed: R1.1, R2.2, U2.2 (-)
unnamed: R3.1, R5.2, U2.6 (-)
V_IN: INPUT.1, R1.2
V_OUT: OUTPUT.1, OUTPUT.2, OUTPUT.3, OUTPUT.4, OUTPUT.5, R14.2
