tinkeringjoe/bread-modular/modules/head_out/head_out.kicad_pcb

## KiCad design modules/head_out/head_out.kicad_pcb (2024-10-21)

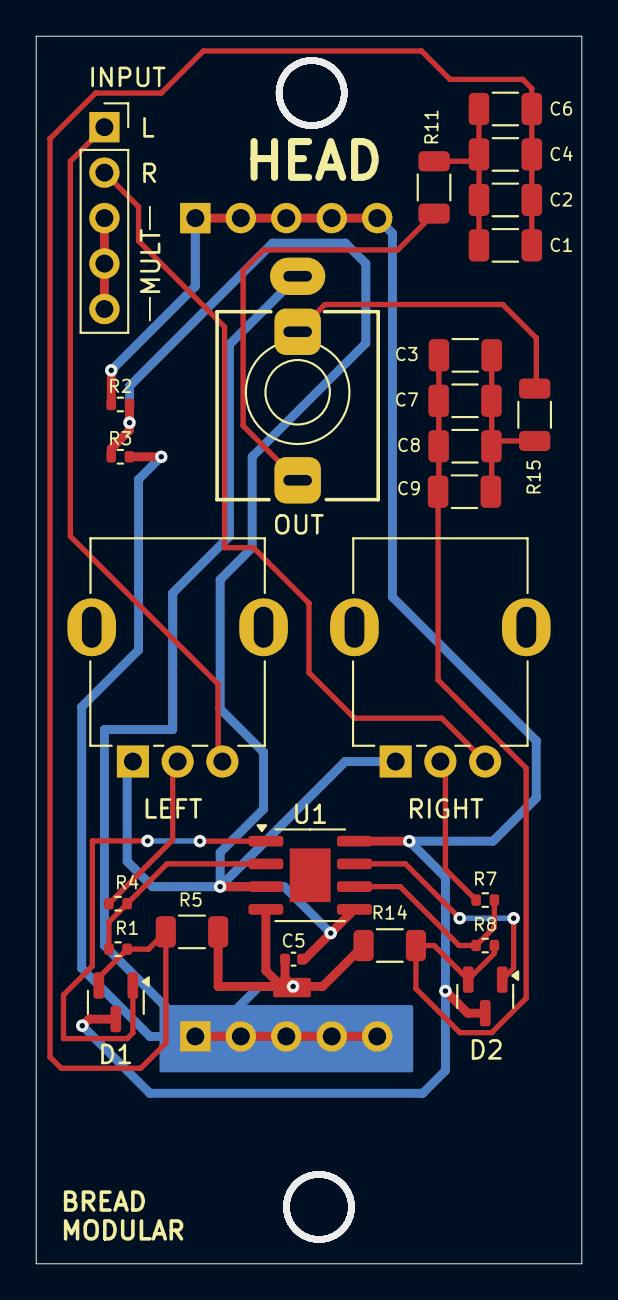
[picture p79: board head_out.kicad_pcb from above]

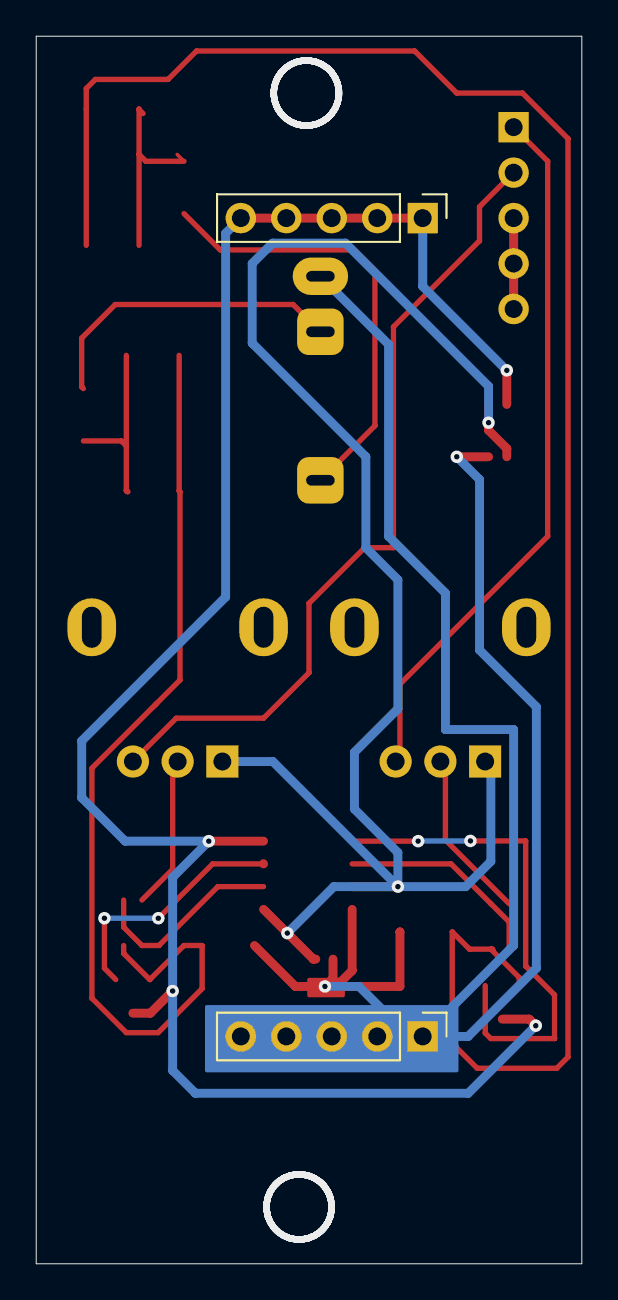
[picture p80: board head_out.kicad_pcb from below]

Board: 2 copper layers, 30.5 x 68.6 mm, 28 parts (2 on the bottom side), 18 nets.

Parts:
5V1: Conn_01x05_Pin; PinHeader_1x05_P2.54mm_Vertical
C1, C2, C3, C4, C6, C7, C8, C9: 100uf; C_1206_3216Metric
C5: 0.1uf; C_0402_1005Metric
D1, D2: SS8050; SOT-23
GND1: Conn_01x05_Pin; PinHeader_1x05_P2.54mm_Vertical
INPUT: Conn_01x05_Socket; PinSocket_1x05_P2.54mm_Vertical
LEFT: 50k; Potentiometer_RV09
OUT: AudioJack3; Jack_3.5mm_QingPu_WQP-PJ366ST_Vertical
R1, R8: 22k; R_0402_1005Metric
R2, R3: 1k; R_0402_1005Metric
R4, R7: 100k; R_0402_1005Metric
R5, R14: 100; R_1206_3216Metric
R11, R15: 10; R_1206_3216Metric
RIGHT: 50k; Potentiometer_RV09
U1: MCP6002-xSN; SOIC-8-1EP_3.9x4.9mm_P1.27mm_EP2.29x3mm

Connections:
+2.5V: C5.2, LEFT.1, R2.2, R3.1, RIGHT.1, U1.3 (+), U1.5 (+)
+5V: 5V1.1, 5V1.2, 5V1.3, 5V1.4, 5V1.5, D1.3 (A), D2.3 (A), R2.1, U1.8 (V+)
GND: C5.1, GND1.1, GND1.2, GND1.3, GND1.4, GND1.5, OUT.S, R3.2, R5.1, R14.1, U1.4 (V-)
IN_L: INPUT.1, LEFT.3
IN_R: INPUT.2, RIGHT.3
unnamed: C1.1, C2.1, C4.1, C6.1, D1.2 (K), R1.2, R5.2
unnamed: C1.2, C2.2, C4.2, C6.2, R11.2
unnamed: C3.1, C7.1, C8.1, C9.1, D2.2 (K), R8.2, R14.2
unnamed: C3.2, C7.2, C8.2, C9.2, R15.2
unnamed: D1.1 (K), U1.1
unnamed: D2.1 (K), U1.7
unnamed: INPUT.3, INPUT.4, INPUT.5
unnamed: LEFT.2, R4.1
unnamed: R7.1, RIGHT.2
unnamed: R1.1, R4.2, U1.2 (-)
unnamed: R7.2, R8.1, U1.6 (-)
OUT_L: OUT.T, R11.1
OUT_R: OUT.R, R15.1
