tinkeringjoe/bread-modular/modules/line_out/line_out.kicad_pcb

## KiCad design modules/line_out/line_out.kicad_pcb (2024-10-18)

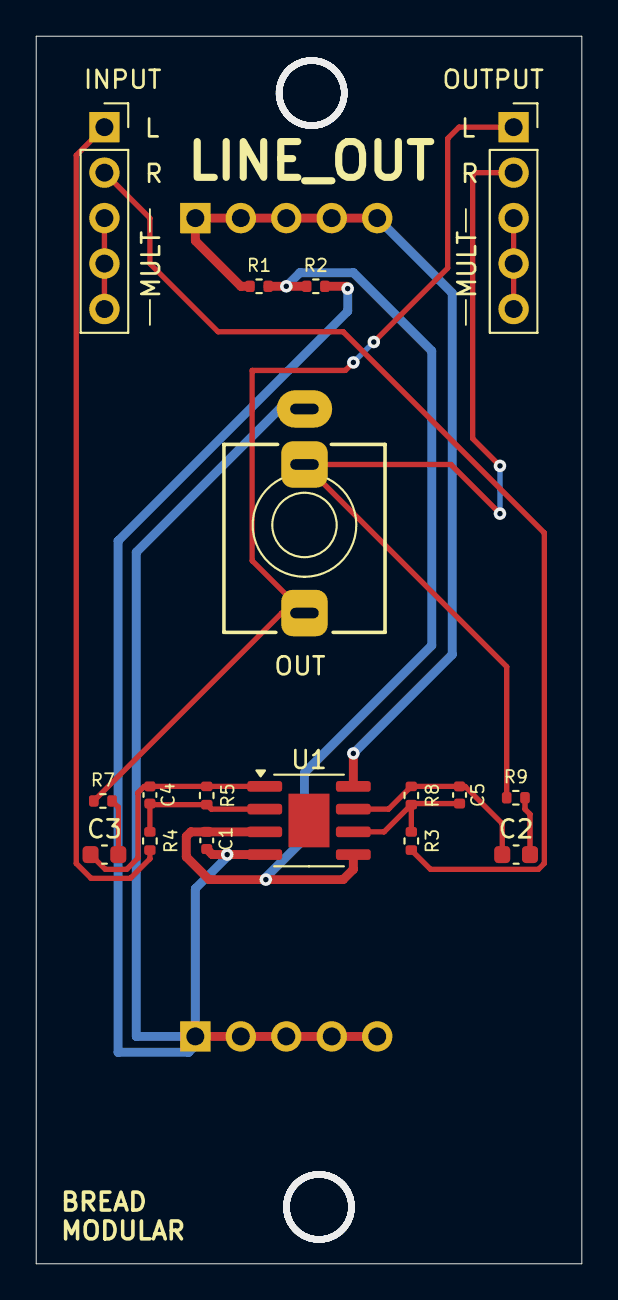
[picture p81: board line_out.kicad_pcb from above]

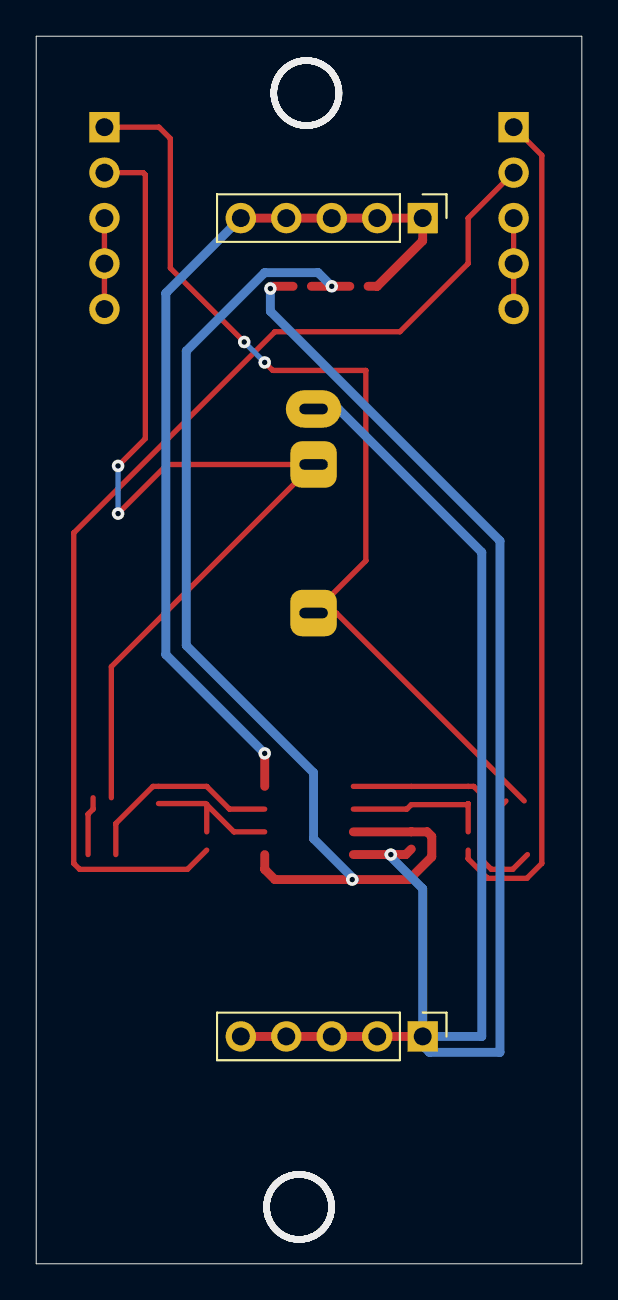
[picture p82: board line_out.kicad_pcb from below]

Board: 2 copper layers, 30.5 x 68.6 mm, 19 parts (2 on the bottom side), 15 nets.

Parts:
5V1: Conn_01x05_Pin; PinHeader_1x05_P2.54mm_Vertical
C1: 0.1uf; C_0402_1005Metric
C2, C3: 2.2uf; C_0603_1608Metric
C4, C5: 100pf; C_0402_1005Metric
GND1: Conn_01x05_Pin; PinHeader_1x05_P2.54mm_Vertical
INPUT: Conn_01x05_Socket; PinSocket_1x05_P2.54mm_Vertical
OUT: AudioJack3; Jack_3.5mm_QingPu_WQP-PJ366ST_Vertical
OUTPUT: Conn_01x05_Socket; PinSocket_1x05_P2.54mm_Vertical
R1, R2, R7, R9: 1k; R_0402_1005Metric
R3, R4: 100k; R_0402_1005Metric
R5, R8: 33k; R_0402_1005Metric
U1: TL072; SOIC-8-1EP_3.9x4.9mm_P1.27mm_EP2.29x3mm

Connections:
+2.5V: C1.2, R1.2, R2.1, U1.3 (+), U1.5 (+)
+5V: 5V1.1, 5V1.2, 5V1.3, 5V1.4, 5V1.5, R1.1, U1.8 (V+)
GND: C1.1, GND1.1, GND1.2, GND1.3, GND1.4, GND1.5, OUT.S, R2.2, U1.4 (V-)
IN_L: INPUT.1, R4.2
IN_R: INPUT.2, R3.2
unnamed: C2.1, C5.1, R8.1, U1.7
unnamed: C2.2, R9.2
unnamed: C3.1, C4.1, R5.1, U1.1
unnamed: C3.2, R7.2
unnamed: INPUT.3, INPUT.4, INPUT.5
unnamed: OUTPUT.3, OUTPUT.4, OUTPUT.5
unnamed: C4.2, R4.1, R5.2, U1.2 (-)
unnamed: C5.2, R3.1, R8.2, U1.6 (-)
OUT_L: OUT.T, OUTPUT.1, R7.1
OUT_R: OUT.R, OUTPUT.2, R9.1
