tinkeringjoe/bread-modular/modules/mco/code/mco/include/tones.h

// Setup the tone1 which will be sent to the PB4
void setupTone1();
void setTone1Frequency(int freq);

// Setup the tone1 which will be sent to the PB5
void setupTone2();
void setTone2Frequency(int freq);
